atechofficials/espnow-mesh-system/esp32-gateway/gateway_v1/hardware/Development_Resources/esp32-s3/esp32_s3_devkit/ESP32-S3-DEV-KIT-N8R8_Pinout.jpg

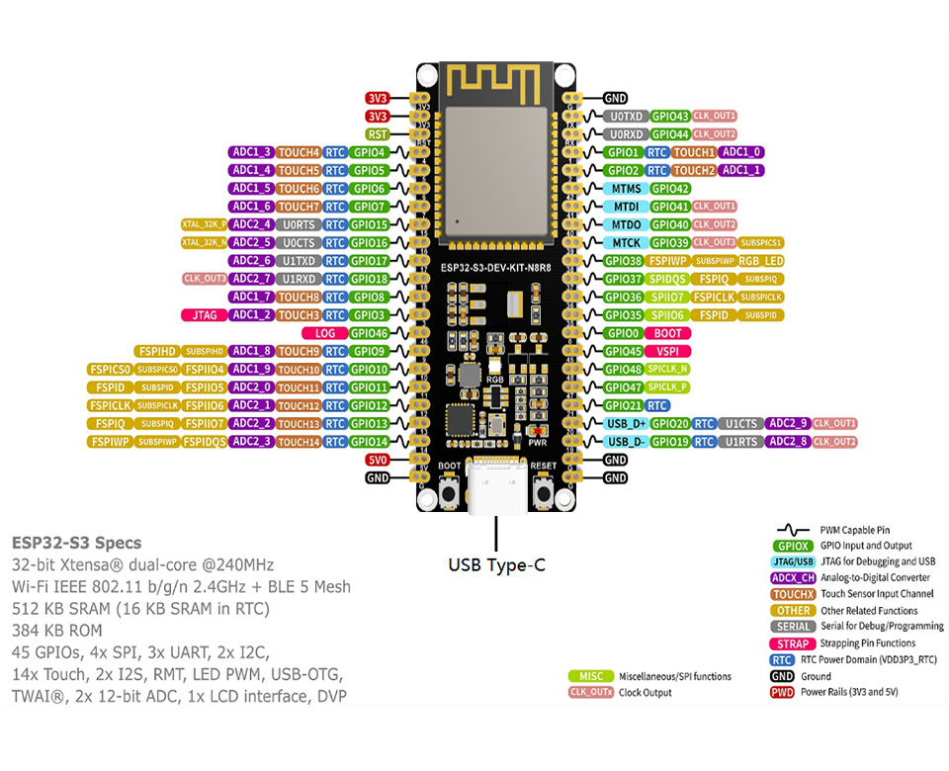
esp32-gateway/gateway_v1/hardware/Development_Resources/esp32-s3/esp32_s3_devkit/ESP32-S3-DEV-KIT-N8R8_Pinout.jpg
