atechofficials/espnow-mesh-system/esp32-gateway/gateway_v1/hardware/Development_Resources/esp32-c3/beetle_esp32_c3/Beetle_ESP32-C3_Overview.png

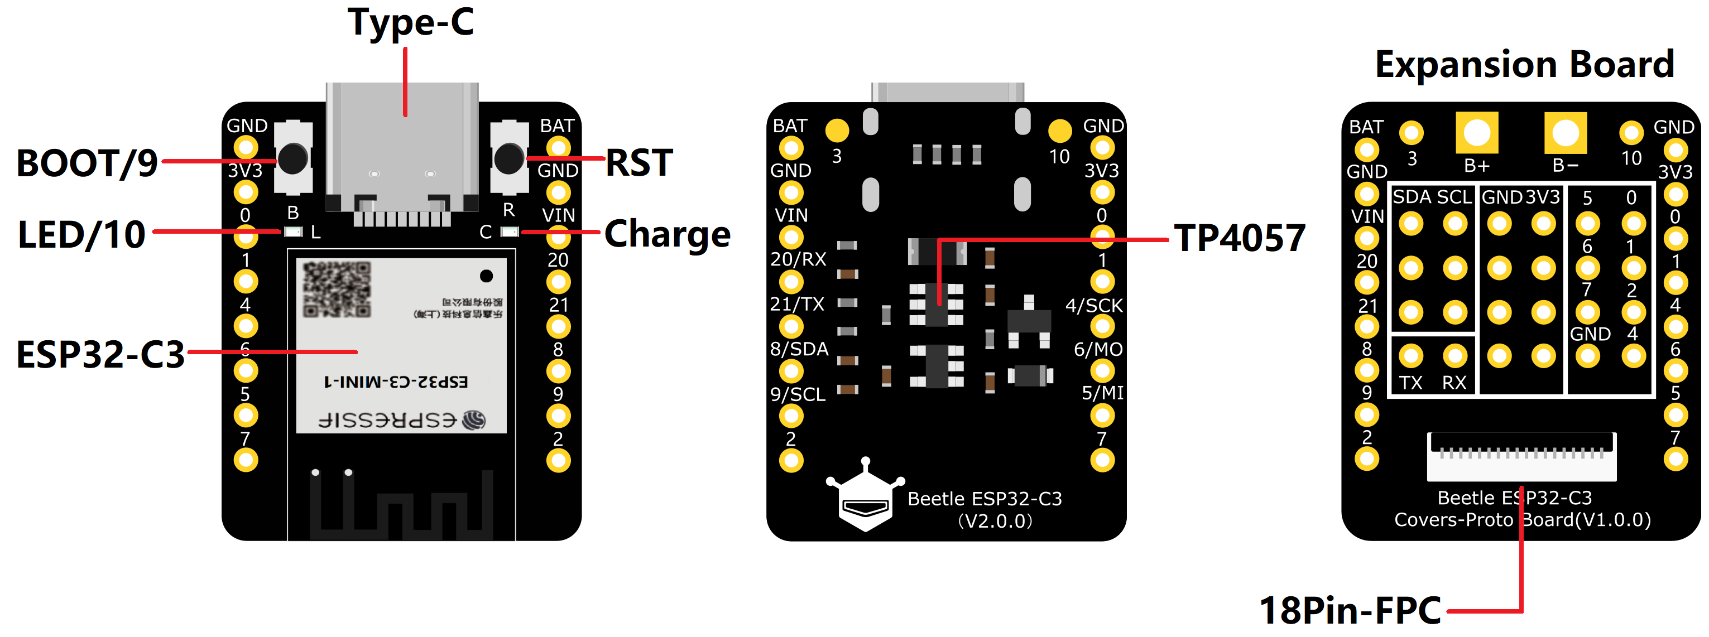
esp32-gateway/gateway_v1/hardware/Development_Resources/esp32-c3/beetle_esp32_c3/Beetle_ESP32-C3_Overview.png
