atechofficials/espnow-mesh-system/esp32-gateway/gateway_v1/src/main.cpp

/**
    * @file [main.cpp]
    * @brief Main source file for the ESP32 Mesh Gateway firmware
 * @version 2.6.7
    * @author Mrinal (@atechofficials)
 */
#define FW_VERSION "2.6.7"

#include <Arduino.h>
#include <WiFi.h>
#include <WiFiClient.h>
#include <WiFiManager.h>
#include <esp_now.h>
#include <esp_wifi.h>
#include <LittleFS.h>
#include <ESPAsyncWebServer.h>
#include <ArduinoJson.h>
#include <PubSubClient.h>
#include <Adafruit_NeoPixel.h>
#include <math.h>
#include <Update.h>
#include <esp_app_format.h>
#include <esp_ota_ops.h>
#include "mesh_protocol.h"
#include "coproc_ota_protocol.h"
#include <Preferences.h>
#include "mbedtls/sha256.h"
#include <algorithm>
#include <ctype.h>
#include <set>
#include "user_config.h"

#if GATEWAY_BUILTIN_SENSOR_ENABLED
    #include <SPI.h>
#endif

#if GATEWAY_BUILTIN_SENSOR_ENABLED
    #include <Adafruit_BME280.h>
    #include <Adafruit_BMP280.h>
#endif

// Other Configuration
#define WEB_PORT         80
#define RELAY_LABEL_MAX_LEN 25
#define OTA_DESC_BUF_LEN (sizeof(esp_image_header_t) + sizeof(esp_image_segment_header_t) + sizeof(esp_app_desc_t))
#define OTA_FW_MARKER "GWFWVER:"
#define OTA_FW_MARKER_LEN 8
#define OTA_FW_VERSION_MAX_LEN 16
#define OTA_HWCFG_MARKER "GWHWCFG:"
#define OTA_HWCFG_MARKER_LEN 8
#define OTA_HWCFG_ID_MAX_LEN HW_CONFIG_ID_LEN
#define OTA_ERROR_MSG_MAX_LEN 192
#define COPROC_BUSY_MSG "Coprocessor Busy. Please try after some time."
#define COPROC_OTA_FW_MARKER "C3FWVER:"
#define COPROC_OTA_FW_MARKER_LEN 8
#define COPROC_OTA_HWCFG_MARKER "C3HWCFG:"
#define COPROC_OTA_HWCFG_MARKER_LEN 8
#define COPROC_OTA_VERSION_MAX_LEN COPROC_FW_VERSION_LEN
#define NODE_OTA_FW_MARKER "NODEFWVER:"
#define NODE_OTA_FW_MARKER_LEN 10
#define NODE_OTA_ROLE_MARKER "NODETYPE:"
#define NODE_OTA_ROLE_MARKER_LEN 9
#define NODE_OTA_HWCFG_MARKER "NODEHWCFG:"
#define NODE_OTA_HWCFG_MARKER_LEN 10
#define NODE_OTA_VERSION_MAX_LEN 16
#define NODE_OTA_FILE_PATH "/node_ota.bin"
#define COPROC_OTA_FILE_PATH "/coproc_ota.bin"
#define NODE_OTA_PORT 80
#define NODE_OTA_AP_CHANNEL 6
#define NODE_OTA_STAGE_TIMEOUT_MS 120000UL
#define NODE_OTA_TRANSFER_TIMEOUT_MS 300000UL
#define NODE_OTA_REJOIN_TIMEOUT_MS 90000UL
#define NODE_OTA_TIMEOUT_RECOVERY_MS 120000UL
#define NODE_OTA_BEGIN_RETRY_MS 2000UL
#define NODE_OTA_BEGIN_MAX_ATTEMPTS 10
#define COPROC_OTA_STAGE_TIMEOUT_MS 120000UL
#define COPROC_OTA_REBOOT_TIMEOUT_MS 90000UL
#define COPROC_UART_BAUD 230400
#define COPROC_UART_RX_BUFFER_SIZE 4096
#define COPROC_UART_TX_BUFFER_SIZE 4096
#define COPROC_LINK_PING_MS 5000UL
#define COPROC_ACK_TIMEOUT_MS 3000UL
#define COPROC_RECOVERY_REBOOT_MS 8000UL
#define COPROC_RECOVERY_COOLDOWN_MS 15000UL
#define COPROC_ACK_RETRY_LIMIT 3
#define COPROC_FRAME_MAX_PAYLOAD sizeof(CoprocUploadChunkPayload)
#define GATEWAY_STA_CONNECT_TIMEOUT_MS 15000UL
#define GATEWAY_NETWORK_MONITOR_MS 2000UL
#define GATEWAY_OFFLINE_RETRY_MS 15000UL
#define GATEWAY_FACTORY_RESET_HOLD_MS 6000UL
#define GATEWAY_FACTORY_RESET_LED_BLINK_MS 300UL
#define MQTT_RECONNECT_MS 10000UL
#define MQTT_BUFFER_SIZE 4096U
#define MQTT_KEEPALIVE_SEC 30U
#define MQTT_SOCKET_TIMEOUT_SEC 5U
#define MQTT_DEFAULT_PORT 1883U
#define MQTT_HA_DISCOVERY_PREFIX "homeassistant"

// Runtime AP credentials - loaded from NVS on boot, fall back to compile-time defaults.
// These are the SSID / password the WiFiManager captive portal AP will use.
static char gwApSsid[33]     = AP_SSID_DEFAULT;
static char gwApPassword[64] = AP_PASS_DEFAULT;
static char gwOfflineSsid[33] = OFFLINE_AP_SSID_DEFAULT;
static char gwOfflinePassword[64] = OFFLINE_AP_PASS_DEFAULT;
static char savedRouterSsid[33] = {0};
static char savedRouterPassword[65] = {0};

// Web Interface Auth
static char webUsername[33]   = "";   // max 32 chars
static char webPassHash[65]   = "";   // SHA-256 hex of password
static char sessionToken[65]  = "";   // generated at login, lives in RAM only
static char rememberToken[65] = "";   // NVS-persisted, used for "Remember Me"
static std::set<uint32_t> authWsClients;  // authenticated WS client IDs

#define RX_QUEUE_SIZE    30
#define WS_UPDATE_MS     2000
#define WS_META_MS       10000
#define DISCOVERED_CLEANUP_MS 1000
#define MAX_DISCOVERED   10
#define RFID_UID_HEX_MAX_LEN ((RFID_UID_MAX_LEN * 2) + 1)

// Node Registry
struct GatewayRfidSlot {
    bool     enabled = false;
    uint8_t  uidLen = 0;
    uint16_t relayMask = 0;
    uint8_t  uid[RFID_UID_MAX_LEN] = {0};
};

struct NodeRecord {
    uint8_t       mac[6];
    NodeType      type;
    uint32_t      capabilities;
    char          name[MESH_NODE_NAME_LEN];
    char          fw_version[8];  // reported by node in MSG_REGISTER
    char          hw_config_id[HW_CONFIG_ID_LEN];  // reported by node in MSG_REGISTER
    unsigned long lastSeen;
    bool          online;
    uint32_t      uptime;
    uint8_t actuatorMask;
    uint8_t       actuatorCount;
    // Per-node dynamic settings schema (populated by MSG_SETTINGS_DATA)
    uint8_t       settingsCount;                     // 0 = not yet received
    SettingDef    settings[NODE_MAX_SETTINGS];        // schema + current values
    // Per-node dynamic sensor schema (populated by MSG_SENSOR_SCHEMA)
    // Indexed by position; sensorSchema[j] and sensorValues[j] are always parallel.
    // sensorCount == 0 means schema has not yet been received from this node.
    uint8_t       sensorCount;                       // 0 = schema not yet received
    SensorDef     sensorSchema[NODE_MAX_SENSORS];    // descriptor for each sensor channel
    float         sensorValues[NODE_MAX_SENSORS];    // last received value per channel
    ActuatorDef   actuatorSchema[NODE_MAX_ACTUATORS];
    char          relayLabels[NODE_MAX_ACTUATORS][RELAY_LABEL_MAX_LEN];
    bool          rfidConfigReady;
    GatewayRfidSlot rfidSlots[RFID_MAX_SLOTS];
    uint8_t       lastRfidUid[RFID_UID_MAX_LEN];
    uint8_t       lastRfidUidLen;
    int8_t        lastRfidMatchedSlot;
    uint16_t      lastRfidAppliedMask;
    unsigned long lastRfidSeenAt;
};
static NodeRecord nodes[MESH_MAX_NODES + 1];
static uint8_t    nextId = 1;
static bool       nodeRegistryDirty = false;
static unsigned long nodeRegistryDirtyAtMs = 0;
static constexpr unsigned long NODE_REGISTRY_FLUSH_MS = 750UL;

// Discovered (beaconing) nodes - not yet paired
struct DiscoveredNode {
    uint8_t       mac[6];
    char          name[MESH_NODE_NAME_LEN];
    NodeType      type;
    uint8_t       tx_channel;  // channel from last beacon
    unsigned long lastSeen;
    bool          active;
};
static DiscoveredNode discovered[MAX_DISCOVERED];

// Pending pair - gateway retries PAIR_CMD until MSG_REGISTER arrives
struct PendingPair {
    uint8_t       mac[6];
    bool          active;
    unsigned long startedAt;
    unsigned long lastAttempt;
};
static PendingPair pendingPair = {};

// RTOS
static SemaphoreHandle_t nodesMutex;

struct RxPacket { uint8_t mac[6]; uint8_t data[250]; int len; };
static QueueHandle_t rxQueue;

// Web Server
static AsyncWebServer server(WEB_PORT);
static AsyncWebSocket ws("/ws");

enum GatewayNetworkMode : uint8_t {
    GATEWAY_SETUP_PORTAL = 0,
    GATEWAY_ONLINE_STA,
    GATEWAY_OFFLINE_AP,
};

// State
static uint8_t   wifiChannel = 1;
static uint32_t  bootMs      = 0;
static GatewayNetworkMode gatewayNetworkMode = GATEWAY_SETUP_PORTAL;
static bool gatewayRouterCredsSaved = false;
static bool gatewayRouterOnline = false;
static bool gatewayOfflineApActive = false;
static bool gatewayManualOfflinePreferred = false;
static bool gatewayForceSetupPortalNextBoot = false;
static bool gatewayOfflineAutoFallback = false;
static uint8_t gatewayLastKnownChannel = OFFLINE_AP_DEFAULT_CHANNEL;
static unsigned long lastGatewayNetworkCheckAt = 0;
static unsigned long lastGatewayRouterRetryAt = 0;
static bool gatewayRouterRetryInProgress = false;
static bool gatewayResetButtonReleased = false;
static bool gatewayResetButtonHandled = false;
static unsigned long gatewayResetButtonPressedAt = 0;
static const IPAddress GATEWAY_OFFLINE_AP_IP(192, 168, 8, 1);
static const IPAddress GATEWAY_OFFLINE_AP_GATEWAY(192, 168, 8, 1);
static const IPAddress GATEWAY_OFFLINE_AP_SUBNET(255, 255, 255, 0);

// Gateway Status LED
static Adafruit_NeoPixel gwLed(1, GW_LED_PIN, GW_LED_COL_ORDER + NEO_KHZ800);
static uint32_t          gwLedCurrent   = 0xDEADBEEF;
static uint32_t          gwLedDesiredColor = 0;
static unsigned long     gwLedFlashUntil = 0;
bool gwLedEnabled = true;
enum GatewayLedOverrideMode : uint8_t {
    GW_LED_OVERRIDE_NONE = 0,
    GW_LED_OVERRIDE_FACTORY_RESET_BLINK,
    GW_LED_OVERRIDE_FACTORY_RESET_SOLID,
};
static GatewayLedOverrideMode gwLedOverrideMode = GW_LED_OVERRIDE_NONE;
static unsigned long     gwLedOverrideLastBlinkAt = 0;
static bool              gwLedOverrideBlinkOn = false;

enum GatewayBuiltinSensorTempUnit : uint8_t {
    GATEWAY_SENSOR_TEMP_C = 0,
    GATEWAY_SENSOR_TEMP_F,
};

enum GatewayBuiltinSensorAltitudeUnit : uint8_t {
    GATEWAY_SENSOR_ALT_M = 0,
    GATEWAY_SENSOR_ALT_FT,
};

enum GatewayBuiltinSensorModel : uint8_t {
    GATEWAY_BUILTIN_SENSOR_MODEL_UNKNOWN = 0,
    GATEWAY_BUILTIN_SENSOR_MODEL_BMP280,
    GATEWAY_BUILTIN_SENSOR_MODEL_BME280,
};

static bool gatewayBuiltinSensorPresent = false;
static GatewayBuiltinSensorModel gatewayBuiltinSensorModel = GATEWAY_BUILTIN_SENSOR_MODEL_UNKNOWN;
static float gatewayBuiltinSensorTempC = NAN;
static float gatewayBuiltinSensorPressureHpa = NAN;
static float gatewayBuiltinSensorHumidity = NAN;
static unsigned long gatewayBuiltinSensorLastSampleAt = 0;
static GatewayBuiltinSensorTempUnit gatewayBuiltinSensorTempUnit = GATEWAY_SENSOR_TEMP_C;
static GatewayBuiltinSensorAltitudeUnit gatewayBuiltinSensorAltitudeUnit = GATEWAY_SENSOR_ALT_M;
static float gatewayBuiltinSensorAltitudeMeters = 0.0f;
static bool gatewayBuiltinSensorAltitudeConfigured = false;

// MQTT Bridge
static WiFiClient mqttNetClient;
static PubSubClient mqttClient(mqttNetClient);
static bool mqttEnabled = false;
static bool mqttConnected = false;
static char mqttHost[65] = {0};
static uint16_t mqttPort = MQTT_DEFAULT_PORT;
static char mqttBaseTopic[97] = "esp32/mesh";
static char mqttUsername[65] = {0};
static char mqttPassword[65] = {0};
static bool mqttHasPassword = false;
static char mqttLastError[128] = {0};
static unsigned long lastMqttReconnectAttemptAt = 0;
static unsigned long lastMqttMetaPublishAt = 0;
static bool mqttRepublishAllPending = false;
static bool mqttMetaDirty = false;
static bool mqttGatewayControlDiscoveryDirty = false;
static bool mqttBuiltinDiscoveryDirty = false;
static bool mqttBuiltinStateDirty = false;
static uint32_t mqttNodeDiscoveryDirtyMask = 0;
static uint32_t mqttNodeSummaryDirtyMask = 0;
static uint32_t mqttNodeSensorStateDirtyMask = 0;
static uint32_t mqttNodeActuatorStateDirtyMask = 0;
static uint32_t mqttNodeSettingsStateDirtyMask = 0;
static uint32_t mqttNodeHeldSensorStateMask[MESH_MAX_NODES + 1] = {0};
static char mqttGatewayTopicId[13] = {0};
static bool mqttLastShouldBeConnected = false;

struct MqttRemovedNodeSnapshot {
    bool active = false;
    char macId[13] = {0};
    bool hadSensors = false;
    uint8_t sensorCount = 0;
    uint8_t sensorIds[NODE_MAX_SENSORS] = {0};
    bool hadActuators = false;
    uint8_t actuatorCount = 0;
    uint8_t actuatorIds[NODE_MAX_ACTUATORS] = {0};
    uint8_t settingsCount = 0;
    uint8_t settingIds[NODE_MAX_SETTINGS] = {0};
    SettingType settingTypes[NODE_MAX_SETTINGS] = {};
};
static MqttRemovedNodeSnapshot mqttRemovedNodes[MESH_MAX_NODES];

#if GATEWAY_BUILTIN_SENSOR_ENABLED
static SPIClass gatewayBuiltinSensorSpi(FSPI);
static bool gatewayBuiltinSensorSpiReady = false;
static Adafruit_BME280 gatewayBuiltinBme(BME_CS, &gatewayBuiltinSensorSpi);
static Adafruit_BMP280 gatewayBuiltinBmp(BME_CS, &gatewayBuiltinSensorSpi);
#endif

__attribute__((used)) static const char kGatewayFirmwareVersionMarker[] = OTA_FW_MARKER FW_VERSION;
__attribute__((used)) static const char kGatewayHardwareConfigMarker[] = OTA_HWCFG_MARKER HW_CONFIG_ID;
static volatile uint32_t gGatewayFirmwareMarkerChecksum = 0;

static void touchGatewayFirmwareMarkers() {
    uint32_t sum = 0;
    for (size_t i = 0; kGatewayFirmwareVersionMarker[i] != '\0'; i++) {
        sum += (uint8_t)kGatewayFirmwareVersionMarker[i];
    }
    for (size_t i = 0; kGatewayHardwareConfigMarker[i] != '\0'; i++) {
        sum += (uint8_t)kGatewayHardwareConfigMarker[i];
    }
    gGatewayFirmwareMarkerChecksum = sum;
}

struct GatewayOtaRequestState {
    bool   started = false;
    bool   ok = false;
    bool   updateBegun = false;
    bool   metadataValidated = false;
    bool   descFlushed = false;
    size_t expectedSize = 0;
    size_t written = 0;
    char   filename[64] = {0};
    char   incomingVersion[33] = {0};
    char   incomingDisplayVersion[OTA_FW_VERSION_MAX_LEN] = {0};
    char   incomingHwConfigId[OTA_HWCFG_ID_MAX_LEN] = {0};
    char   error[OTA_ERROR_MSG_MAX_LEN] = {0};
    uint8_t descBuf[OTA_DESC_BUF_LEN] = {0};
    size_t descBytes = 0;
    uint8_t markerMatchIndex = 0;
    bool    markerReadingVersion = false;
    uint8_t markerVersionLen = 0;
    uint8_t hwMarkerMatchIndex = 0;
    bool    hwMarkerReading = false;
    uint8_t hwMarkerLen = 0;
};

enum CoprocOtaJobStage : uint8_t {
    COPROC_OTA_JOB_IDLE = 0,
    COPROC_OTA_JOB_STAGED,
    COPROC_OTA_JOB_WAIT_HELLO,
    COPROC_OTA_JOB_BEGIN,
    COPROC_OTA_JOB_STREAM,
    COPROC_OTA_JOB_FINALIZE,
    COPROC_OTA_JOB_WAIT_REBOOT,
    COPROC_OTA_JOB_SUCCESS,
    COPROC_OTA_JOB_ERROR,
};

struct CoprocOtaUploadRequestState {
    bool   started = false;
    bool   ok = false;
    bool   metadataValidated = false;
    size_t expectedSize = 0;
    size_t written = 0;
    uint32_t crc32 = 0xFFFFFFFFu;
    char   filename[64] = {0};
    char   incomingVersion[33] = {0};
    char   incomingDisplayVersion[COPROC_OTA_VERSION_MAX_LEN] = {0};
    char   incomingHwConfigId[HW_CONFIG_ID_LEN] = {0};
    char   incomingProjectName[COPROC_PROJECT_NAME_LEN] = {0};
    char   error[OTA_ERROR_MSG_MAX_LEN] = {0};
    uint8_t descBuf[OTA_DESC_BUF_LEN] = {0};
    size_t descBytes = 0;
    uint8_t versionMarkerMatchIndex = 0;
    bool    versionMarkerReading = false;
    uint8_t versionMarkerLen = 0;
    uint8_t hwMarkerMatchIndex = 0;
    bool    hwMarkerReading = false;
    uint8_t hwMarkerLen = 0;
    File    file;
};

static bool          otaUploadBusy    = false;
static bool          otaRebootPending = false;
static unsigned long otaRebootAtMs    = 0;

enum NodeOtaJobStage : uint8_t {
    NODE_OTA_JOB_IDLE = 0,
    NODE_OTA_JOB_STAGED,
    NODE_OTA_JOB_COPROC_WAIT,
    NODE_OTA_JOB_COPROC_BEGIN,
    NODE_OTA_JOB_COPROC_STREAM,
    NODE_OTA_JOB_COPROC_FINALIZE,
    NODE_OTA_JOB_SEND_COMMAND,
    NODE_OTA_JOB_WAIT_TRANSFER,
    NODE_OTA_JOB_WAIT_REJOIN,
    NODE_OTA_JOB_SUCCESS,
    NODE_OTA_JOB_ERROR,
};

struct NodeOtaUploadRequestState {
    bool   started = false;
    bool   ok = false;
    bool   metadataValidated = false;
    bool   descFlushed = false;
    size_t expectedSize = 0;
    size_t written = 0;
    uint32_t crc32 = 0xFFFFFFFFu;
    char   filename[64] = {0};
    char   incomingVersion[NODE_OTA_VERSION_MAX_LEN] = {0};
    char   incomingDisplayVersion[NODE_OTA_VERSION_MAX_LEN] = {0};
    char   incomingRole[16] = {0};
    char   incomingHwConfigId[HW_CONFIG_ID_LEN] = {0};
    char   error[OTA_ERROR_MSG_MAX_LEN] = {0};
    uint8_t descBuf[OTA_DESC_BUF_LEN] = {0};
    size_t descBytes = 0;
    uint8_t versionMarkerMatchIndex = 0;
    bool    versionMarkerReading = false;
    uint8_t versionMarkerLen = 0;
    uint8_t roleMarkerMatchIndex = 0;
    bool    roleMarkerReading = false;
    uint8_t roleMarkerLen = 0;
    uint8_t hwMarkerMatchIndex = 0;
    bool    hwMarkerReading = false;
    uint8_t hwMarkerLen = 0;
    File    file;
};

struct NodeOtaJobState {
    bool           active = false;
    bool           uploadBusy = false;
    bool           helperOnline = false;
    bool           awaitingAck = false;
    bool           helperApReady = false;
    bool           helperTransferDone = false;
    bool           nodeAccepted = false;
    uint8_t        awaitingFrameType = 0;
    uint8_t        nodeId = 0;
    NodeType       targetType = NODE_SENSOR;
    NodeOtaJobStage stage = NODE_OTA_JOB_IDLE;
    uint32_t       sessionId = 0;
    uint32_t       imageCrc32 = 0;
    size_t         imageSize = 0;
    size_t         uploadOffset = 0;
    unsigned long  lastCommandAt = 0;
    unsigned long  stageStartedAt = 0;
    unsigned long  lastActivityAt = 0;
    unsigned long  lastAckAt = 0;
    uint8_t        coprocAckRetries = 0;
    uint8_t        commandAttempts = 0;
    char           version[NODE_OTA_VERSION_MAX_LEN] = {0};
    char           priorVersion[8] = {0};
    char           filename[64] = {0};
    char           message[96] = {0};
    char           error[128] = {0};
    char           apSsid[NODE_OTA_SSID_LEN] = {0};
    char           apPassword[NODE_OTA_PASS_LEN] = {0};
    uint8_t        progress = 0;
    File           file;
};

struct CoprocOtaJobState {
    bool           active = false;
    bool           uploadBusy = false;
    bool           awaitingAck = false;
    bool           rebootSeen = false;
    bool           flashReportedDone = false;
    uint8_t        awaitingFrameType = 0;
    CoprocOtaJobStage stage = COPROC_OTA_JOB_IDLE;
    uint32_t       sessionId = 0;
    uint32_t       imageCrc32 = 0;
    size_t         imageSize = 0;
    size_t         uploadOffset = 0;
    unsigned long  stageStartedAt = 0;
    unsigned long  lastActivityAt = 0;
    unsigned long  lastAckAt = 0;
    uint8_t        ackRetries = 0;
    char           version[COPROC_OTA_VERSION_MAX_LEN] = {0};
    char           priorVersion[COPROC_FW_VERSION_LEN] = {0};
    char           filename[64] = {0};
    char           message[96] = {0};
    char           error[128] = {0};
    uint8_t        progress = 0;
    File           file;
};

struct CoprocAckState {
    bool     ready = false;
    uint8_t  originalType = 0;
    bool     ok = false;
    uint32_t value = 0;
    char     message[COPROC_STATUS_MESSAGE_LEN] = {0};
};

struct CoprocRxState {
    enum State : uint8_t {
        WAIT_MAGIC_1 = 0,
        WAIT_MAGIC_2,
        READ_TYPE,
        READ_LEN_1,
        READ_LEN_2,
        READ_PAYLOAD,
        READ_CRC_1,
        READ_CRC_2,
    } state = WAIT_MAGIC_1;
    uint8_t  type = 0;
    uint16_t length = 0;
    uint16_t expectedCrc = 0;
    uint16_t payloadIndex = 0;
    uint8_t  payload[COPROC_FRAME_MAX_PAYLOAD] = {0};
};

static HardwareSerial coprocSerial(1);
static NodeOtaJobState nodeOtaJob;
static CoprocOtaJobState coprocOtaJob;
static CoprocAckState coprocAck;
static CoprocRxState coprocRx;
static unsigned long lastCoprocHelloAt = 0;
static bool coprocOnline = false;
static unsigned long lastCoprocAckAt = 0;
static unsigned long lastCoprocNoAckLogAt = 0;
static unsigned long lastCoprocRecoveryPulseAt = 0;
static bool coprocOtaSupportedRemote = false;
static bool espNowReady = false;
static uint32_t coprocOtaMaxBytes = 0;
static char coprocFwVersion[COPROC_FW_VERSION_LEN] = {0};
static char coprocHwConfigId[COPROC_HWCFG_ID_LEN] = {0};
static char coprocProjectName[COPROC_PROJECT_NAME_LEN] = {0};

// *****************************************************************************
// Gateway Status LED Helpers
// *****************************************************************************
static void applyGwLedHardware(uint32_t color) {
    if (color == gwLedCurrent) return;
    gwLedCurrent = color;
    gwLed.setPixelColor(0, color);
    gwLed.show();
}

static void setGwLed(uint32_t color) {
    gwLedDesiredColor = color;
    if (gwLedOverrideMode != GW_LED_OVERRIDE_NONE) return;
    applyGwLedHardware(color);
}

static void startGatewayFactoryResetLedBlink(unsigned long now) {
    gwLedOverrideMode = GW_LED_OVERRIDE_FACTORY_RESET_BLINK;
    gwLedOverrideLastBlinkAt = now;
    gwLedOverrideBlinkOn = true;
    applyGwLedHardware(gwLed.Color(160, 60, 0));  // dark orange
}

static void showGatewayFactoryResetLedConfirm() {
    gwLedOverrideMode = GW_LED_OVERRIDE_FACTORY_RESET_SOLID;
    gwLedOverrideBlinkOn = true;
    applyGwLedHardware(gwLed.Color(255, 0, 0));  // solid red
}

static void clearGatewayLedOverride() {
    if (gwLedOverrideMode == GW_LED_OVERRIDE_NONE) return;
    gwLedOverrideMode = GW_LED_OVERRIDE_NONE;
    gwLedOverrideBlinkOn = false;
    gwLedCurrent = 0xDEADBEEF;  // force immediate repaint from normal state
    if (!gwLedEnabled) {
        applyGwLedHardware(0);
        return;
    }
    if (millis() < gwLedFlashUntil) {
        applyGwLedHardware(gwLedDesiredColor);
        return;
    }
    setGwLed(gwLed.Color(0, 0, 32));  // resume normal operational color
}

static void flashGwLed(uint32_t color, uint32_t durationMs) {
    gwLedFlashUntil = millis() + durationMs;
    setGwLed(color);
    gwLedCurrent = 0xDEADBEEF;  // force refresh after flash
}

static void updateGwLed() {
    const unsigned long now = millis();

    if (gwLedOverrideMode == GW_LED_OVERRIDE_FACTORY_RESET_SOLID) {
        applyGwLedHardware(gwLed.Color(255, 0, 0));
        return;
    }

    if (gwLedOverrideMode == GW_LED_OVERRIDE_FACTORY_RESET_BLINK) {
        if ((now - gwLedOverrideLastBlinkAt) >= GATEWAY_FACTORY_RESET_LED_BLINK_MS) {
            gwLedOverrideLastBlinkAt = now;
            gwLedOverrideBlinkOn = !gwLedOverrideBlinkOn;
        }
        applyGwLedHardware(gwLedOverrideBlinkOn ? gwLed.Color(160, 60, 0) : 0);
        return;
    }

    if (!gwLedEnabled) {
        applyGwLedHardware(0);
        return;
    }
    if (now < gwLedFlashUntil) {
        applyGwLedHardware(gwLedDesiredColor);
        return;
    }
    setGwLed(gwLed.Color(0, 0, 32));  // dim blue = operational
}

static void saveGwLedState(bool enabled) {
    Preferences prefs;
    prefs.begin("gwconfig", false);  // read-write
    prefs.putBool("led_enabled", enabled);
    prefs.end();
    gwLedEnabled = enabled;
    if (!enabled && gwLedOverrideMode == GW_LED_OVERRIDE_NONE) {
        setGwLed(0);  // turn off immediately
    }
}

static void loadGwLedState() {
    Preferences prefs;
    prefs.begin("gwconfig", true);  // read-only
    gwLedEnabled = prefs.getBool("led_enabled", true);
    prefs.end();
    Serial.printf("[CFG]  Gateway LED is %s\n", gwLedEnabled ? "enabled" : "disabled");
    if (!gwLedEnabled && gwLedOverrideMode == GW_LED_OVERRIDE_NONE) {
        setGwLed(0);
    }
}

// *****************************************************************************
//  Gateway Built-in Sensor Helpers
// *****************************************************************************
static void mqttMarkBuiltinDiscoveryDirty();
static void mqttMarkBuiltinStateDirty();
static void mqttMarkMetaDirty();

static bool gatewayBuiltinSensorFeatureEnabled() {
    return GATEWAY_BUILTIN_SENSOR_ENABLED;
}

static const char* gatewayBuiltinSensorModelString() {
    if (!gatewayBuiltinSensorFeatureEnabled()) return "disabled";
    switch (gatewayBuiltinSensorModel) {
        case GATEWAY_BUILTIN_SENSOR_MODEL_BME280: return "bme280";
        case GATEWAY_BUILTIN_SENSOR_MODEL_BMP280: return "bmp280";
        default: return "auto";
    }
}

static bool gatewayBuiltinSensorSupportsHumidity() {
    return gatewayBuiltinSensorModel == GATEWAY_BUILTIN_SENSOR_MODEL_BME280;
}

static const char* gatewayBuiltinSensorTempUnitString() {
    return gatewayBuiltinSensorTempUnit == GATEWAY_SENSOR_TEMP_F ? "F" : "C";
}

static const char* gatewayBuiltinSensorAltitudeUnitString() {
    return gatewayBuiltinSensorAltitudeUnit == GATEWAY_SENSOR_ALT_FT ? "ft" : "m";
}

static bool parseGatewayBuiltinTempUnit(const char* value,
                                        GatewayBuiltinSensorTempUnit* outUnit) {
    if (!outUnit || !value) return false;
    if (strcmp(value, "F") == 0 || strcmp(value, "f") == 0) {
        *outUnit = GATEWAY_SENSOR_TEMP_F;
        return true;
    }
    if (strcmp(value, "C") == 0 || strcmp(value, "c") == 0) {
        *outUnit = GATEWAY_SENSOR_TEMP_C;
        return true;
    }
    return false;
}

static bool parseGatewayBuiltinAltitudeUnit(const char* value,
                                            GatewayBuiltinSensorAltitudeUnit* outUnit) {
    if (!outUnit || !value) return false;
    if (strcmp(value, "ft") == 0 || strcmp(value, "FT") == 0 ||
        strcmp(value, "feet") == 0 || strcmp(value, "Feet") == 0) {
        *outUnit = GATEWAY_SENSOR_ALT_FT;
        return true;
    }
    if (strcmp(value, "m") == 0 || strcmp(value, "M") == 0 ||
        strcmp(value, "meter") == 0 || strcmp(value, "meters") == 0) {
        *outUnit = GATEWAY_SENSOR_ALT_M;
        return true;
    }
    return false;
}

static float gatewayBuiltinAltitudeDisplayValue() {
    if (!isfinite(gatewayBuiltinSensorAltitudeMeters)) return 0.0f;
    if (gatewayBuiltinSensorAltitudeUnit == GATEWAY_SENSOR_ALT_FT) {
        return gatewayBuiltinSensorAltitudeMeters * 3.2808399f;
    }
    return gatewayBuiltinSensorAltitudeMeters;
}

static float gatewayBuiltinAltitudeMetersFromDisplay(float value,
                                                     GatewayBuiltinSensorAltitudeUnit unit) {
    if (!isfinite(value)) return 0.0f;
    return unit == GATEWAY_SENSOR_ALT_FT ? (value / 3.2808399f) : value;
}

static float gatewayBuiltinDisplayTemperature() {
    if (!isfinite(gatewayBuiltinSensorTempC)) return NAN;
    if (gatewayBuiltinSensorTempUnit == GATEWAY_SENSOR_TEMP_F) {
        return (gatewayBuiltinSensorTempC * 9.0f / 5.0f) + 32.0f;
    }
    return gatewayBuiltinSensorTempC;
}

static float gatewayBuiltinSeaLevelPressureHpa() {
    if (!isfinite(gatewayBuiltinSensorPressureHpa) || gatewayBuiltinSensorPressureHpa <= 0.0f) {
        return NAN;
    }
    const float ratio = 1.0f - (gatewayBuiltinSensorAltitudeMeters / 44330.0f);
    if (ratio <= 0.0f) return gatewayBuiltinSensorPressureHpa;
    return gatewayBuiltinSensorPressureHpa / powf(ratio, 5.255f);
}

static void loadGatewayBuiltinSensorSettings() {
    Preferences prefs;
    prefs.begin("gwconfig", true);
    const uint8_t tempUnit = prefs.isKey("bs_temp_u")
        ? prefs.getUChar("bs_temp_u", (uint8_t)GATEWAY_SENSOR_TEMP_C)
        : (uint8_t)GATEWAY_SENSOR_TEMP_C;
    const uint8_t altitudeUnit = prefs.isKey("bs_alt_u")
        ? prefs.getUChar("bs_alt_u", (uint8_t)GATEWAY_SENSOR_ALT_M)
        : (uint8_t)GATEWAY_SENSOR_ALT_M;
    const bool altitudeConfigured = prefs.isKey("bs_alt_m");
    const float altitudeMeters = altitudeConfigured ? prefs.getFloat("bs_alt_m", 0.0f) : 0.0f;
    prefs.end();

    gatewayBuiltinSensorTempUnit = tempUnit == (uint8_t)GATEWAY_SENSOR_TEMP_F
        ? GATEWAY_SENSOR_TEMP_F
        : GATEWAY_SENSOR_TEMP_C;
    gatewayBuiltinSensorAltitudeUnit = altitudeUnit == (uint8_t)GATEWAY_SENSOR_ALT_FT
        ? GATEWAY_SENSOR_ALT_FT
        : GATEWAY_SENSOR_ALT_M;
    gatewayBuiltinSensorAltitudeMeters = isfinite(altitudeMeters)
        ? constrain(altitudeMeters, -500.0f, 10000.0f)
        : 0.0f;
    gatewayBuiltinSensorAltitudeConfigured = altitudeConfigured;
}

static void saveGatewayBuiltinSensorSettings(GatewayBuiltinSensorTempUnit tempUnit,
                                             GatewayBuiltinSensorAltitudeUnit altitudeUnit,
                                             float altitudeMeters) {
    Preferences prefs;
    prefs.begin("gwconfig", false);
    prefs.putUChar("bs_temp_u", (uint8_t)tempUnit);
    prefs.putUChar("bs_alt_u", (uint8_t)altitudeUnit);
    prefs.putFloat("bs_alt_m", altitudeMeters);
    prefs.end();

    gatewayBuiltinSensorTempUnit = tempUnit;
    gatewayBuiltinSensorAltitudeUnit = altitudeUnit;
    gatewayBuiltinSensorAltitudeMeters = altitudeMeters;
    gatewayBuiltinSensorAltitudeConfigured = true;
    mqttMarkBuiltinDiscoveryDirty();
    mqttMarkBuiltinStateDirty();
    mqttMarkMetaDirty();
}

#if GATEWAY_BUILTIN_SENSOR_ENABLED
static bool gatewayBuiltinSensorEnsureSpiReady() {
    if (gatewayBuiltinSensorSpiReady) return true;

    pinMode(BME_CS, OUTPUT);
    digitalWrite(BME_CS, HIGH);
    gatewayBuiltinSensorSpiReady = gatewayBuiltinSensorSpi.begin(BME_SCK, BME_MISO, BME_MOSI, BME_CS);
    if (!gatewayBuiltinSensorSpiReady) {
        Serial.printf("[GW SENS] Failed to start SPI bus for built-in %s (SCK=%d MISO=%d MOSI=%d CS=%d).\n",
                      gatewayBuiltinSensorModelString(), BME_SCK, BME_MISO, BME_MOSI, BME_CS);
        return false;
    }
    delay(2);
    return true;
}

static uint8_t gatewayBuiltinSensorReadSpiReg(uint8_t reg, uint8_t dataMode) {
    if (!gatewayBuiltinSensorEnsureSpiReady()) return 0xFF;

    gatewayBuiltinSensorSpi.beginTransaction(SPISettings(1000000, MSBFIRST, dataMode));
    digitalWrite(BME_CS, LOW);
    gatewayBuiltinSensorSpi.transfer(reg | 0x80);
    const uint8_t value = gatewayBuiltinSensorSpi.transfer(0x00);
    digitalWrite(BME_CS, HIGH);
    gatewayBuiltinSensorSpi.endTransaction();
    return value;
}

static const char* gatewayBuiltinSensorChipIdDescription(uint8_t chipId) {
    switch (chipId) {
        case 0x60: return "BME280";
        case 0x58: return "BMP280";
        case 0x56:
        case 0x57: return "BMP280-family";
        case 0x00: return "no SPI response (stuck low)";
        case 0xFF: return "no SPI response (stuck high)";
        default:   return "unknown response";
    }
}

static GatewayBuiltinSensorModel gatewayBuiltinSensorModelFromChipId(uint8_t chipId) {
    switch (chipId) {
        case 0x60: return GATEWAY_BUILTIN_SENSOR_MODEL_BME280;
        case 0x56:
        case 0x57:
        case 0x58: return GATEWAY_BUILTIN_SENSOR_MODEL_BMP280;
        default:   return GATEWAY_BUILTIN_SENSOR_MODEL_UNKNOWN;
    }
}

static void logGatewayBuiltinSensorProbe() {
    if (!gatewayBuiltinSensorEnsureSpiReady()) return;

    const uint8_t chipIdMode0 = gatewayBuiltinSensorReadSpiReg(0xD0, SPI_MODE0);
    const uint8_t chipIdMode3 = gatewayBuiltinSensorReadSpiReg(0xD0, SPI_MODE3);
    Serial.printf("[GW SENS] SPI probe for built-in sensor on SCK=%d MISO=%d MOSI=%d CS=%d -> mode0=0x%02X (%s), mode3=0x%02X (%s)\n",
                  BME_SCK, BME_MISO, BME_MOSI, BME_CS,
                  chipIdMode0, gatewayBuiltinSensorChipIdDescription(chipIdMode0),
                  chipIdMode3, gatewayBuiltinSensorChipIdDescription(chipIdMode3));
    const GatewayBuiltinSensorModel probeModel =
        gatewayBuiltinSensorModelFromChipId(chipIdMode0) != GATEWAY_BUILTIN_SENSOR_MODEL_UNKNOWN
            ? gatewayBuiltinSensorModelFromChipId(chipIdMode0)
            : gatewayBuiltinSensorModelFromChipId(chipIdMode3);
    if (probeModel == GATEWAY_BUILTIN_SENSOR_MODEL_BME280) {
        Serial.println("[GW SENS] Probe suggests the module is replying as BME280.");
    } else if (probeModel == GATEWAY_BUILTIN_SENSOR_MODEL_BMP280) {
        Serial.println("[GW SENS] Probe suggests the module is replying as BMP280.");
    }
}
#endif

static bool initGatewayBuiltinSensor() {
    bool spiReady = true;
#if GATEWAY_BUILTIN_SENSOR_ENABLED
    spiReady = gatewayBuiltinSensorEnsureSpiReady();
#endif

    if (!gatewayBuiltinSensorFeatureEnabled()) {
        gatewayBuiltinSensorPresent = false;
        gatewayBuiltinSensorModel = GATEWAY_BUILTIN_SENSOR_MODEL_UNKNOWN;
        gatewayBuiltinSensorTempC = NAN;
        gatewayBuiltinSensorPressureHpa = NAN;
        gatewayBuiltinSensorHumidity = NAN;
        mqttMarkBuiltinDiscoveryDirty();
        mqttMarkBuiltinStateDirty();
        mqttMarkMetaDirty();
        return false;
    }

    gatewayBuiltinSensorPresent = false;
    gatewayBuiltinSensorModel = GATEWAY_BUILTIN_SENSOR_MODEL_UNKNOWN;
    gatewayBuiltinSensorTempC = NAN;
    gatewayBuiltinSensorPressureHpa = NAN;
    gatewayBuiltinSensorHumidity = NAN;

#if GATEWAY_BUILTIN_SENSOR_ENABLED
    uint8_t chipIdMode0 = 0xFF;
    uint8_t chipIdMode3 = 0xFF;
    if (spiReady) {
        chipIdMode0 = gatewayBuiltinSensorReadSpiReg(0xD0, SPI_MODE0);
        chipIdMode3 = gatewayBuiltinSensorReadSpiReg(0xD0, SPI_MODE3);
        gatewayBuiltinSensorModel =
            gatewayBuiltinSensorModelFromChipId(chipIdMode0) != GATEWAY_BUILTIN_SENSOR_MODEL_UNKNOWN
                ? gatewayBuiltinSensorModelFromChipId(chipIdMode0)
                : gatewayBuiltinSensorModelFromChipId(chipIdMode3);

        switch (gatewayBuiltinSensorModel) {
            case GATEWAY_BUILTIN_SENSOR_MODEL_BME280:
                gatewayBuiltinSensorPresent = gatewayBuiltinBme.begin();
                break;
            case GATEWAY_BUILTIN_SENSOR_MODEL_BMP280:
                gatewayBuiltinSensorPresent = gatewayBuiltinBmp.begin();
                break;
            default:
                gatewayBuiltinSensorPresent = false;
                break;
        }
    }
#endif

    if (gatewayBuiltinSensorPresent) {
        Serial.printf("[GW SENS] Built-in %s detected on SPI.\n", gatewayBuiltinSensorModelString());
    } else {
        if (gatewayBuiltinSensorModel != GATEWAY_BUILTIN_SENSOR_MODEL_UNKNOWN) {
            Serial.printf("[GW SENS] Built-in %s probe succeeded, but driver init failed.\n",
                          gatewayBuiltinSensorModelString());
        } else {
            Serial.println("[GW SENS] Built-in BMP280/BME280 sensor not detected.");
        }
#if GATEWAY_BUILTIN_SENSOR_ENABLED
        logGatewayBuiltinSensorProbe();
#endif
    }
    mqttMarkBuiltinDiscoveryDirty();
    mqttMarkBuiltinStateDirty();
    mqttMarkMetaDirty();
    return gatewayBuiltinSensorPresent;
}

static bool sampleGatewayBuiltinSensor() {
    if (!gatewayBuiltinSensorFeatureEnabled() || !gatewayBuiltinSensorPresent) return false;
    gatewayBuiltinSensorLastSampleAt = millis();

    float tempC = NAN;
    float pressurePa = NAN;
    float humidity = NAN;
    switch (gatewayBuiltinSensorModel) {
        case GATEWAY_BUILTIN_SENSOR_MODEL_BME280:
            tempC = gatewayBuiltinBme.readTemperature();
            pressurePa = gatewayBuiltinBme.readPressure();
            humidity = gatewayBuiltinBme.readHumidity();
            break;
        case GATEWAY_BUILTIN_SENSOR_MODEL_BMP280:
            tempC = gatewayBuiltinBmp.readTemperature();
            pressurePa = gatewayBuiltinBmp.readPressure();
            humidity = NAN;
            break;
        default:
            return false;
    }

    if (!isfinite(tempC) || !isfinite(pressurePa) || pressurePa <= 0.0f) {
        Serial.println("[GW SENS] Built-in sensor read failed.");
        return false;
    }

    gatewayBuiltinSensorTempC = tempC;
    gatewayBuiltinSensorPressureHpa = pressurePa / 100.0f;
    gatewayBuiltinSensorHumidity = isfinite(humidity) ? humidity : NAN;
    mqttMarkBuiltinStateDirty();
    mqttMarkMetaDirty();
    return true;
}

static void sampleGatewayBuiltinSensorIfDue(unsigned long now) {
    if (!gatewayBuiltinSensorFeatureEnabled() || !gatewayBuiltinSensorPresent) return;
    if (gatewayBuiltinSensorLastSampleAt == 0 ||
        (now - gatewayBuiltinSensorLastSampleAt) >= WS_META_MS) {
        sampleGatewayBuiltinSensor();
    }
}

// *****************************************************************************
//  Helpers
// *****************************************************************************
static String macToStr(const uint8_t* mac) {
    char buf[18];
    snprintf(buf, sizeof(buf), "%02X:%02X:%02X:%02X:%02X:%02X",
             mac[0], mac[1], mac[2], mac[3], mac[4], mac[5]);
    return String(buf);
}

static unsigned long elapsedSinceMs(unsigned long now, unsigned long then) {
    return (now >= then) ? (now - then) : 0UL;
}

static bool parseMac(const char* str, uint8_t* mac) {
    return sscanf(str, "%hhx:%hhx:%hhx:%hhx:%hhx:%hhx",
                  &mac[0], &mac[1], &mac[2], &mac[3], &mac[4], &mac[5]) == 6;
}

static void defaultRelayLabel(uint8_t relayIdx, char* out, size_t outSize) {
    snprintf(out, outSize, "Relay %u", relayIdx + 1);
}

static void resetRelayLabels(char labels[NODE_MAX_ACTUATORS][RELAY_LABEL_MAX_LEN]) {
    for (uint8_t i = 0; i < NODE_MAX_ACTUATORS; i++) {
        defaultRelayLabel(i, labels[i], RELAY_LABEL_MAX_LEN);
    }
}

static void sanitizeRelayLabel(const char* input, uint8_t relayIdx,
                               char* out, size_t outSize) {
    String label = input ? String(input) : String();
    label.trim();
    if (label.length() == 0) {
        defaultRelayLabel(relayIdx, out, outSize);
        return;
    }
    label.replace("\r", " ");
    label.replace("\n", " ");
    while (label.indexOf("  ") >= 0) label.replace("  ", " ");
    strncpy(out, label.c_str(), outSize - 1);
    out[outSize - 1] = '\0';
}

static void buildRelayLabelPrefKey(const uint8_t* mac, char* key, size_t keySize) {
    snprintf(key, keySize, "%02X%02X%02X%02X%02X%02X",
             mac[0], mac[1], mac[2], mac[3], mac[4], mac[5]);
}

struct RelayLabelRecordV1 {
    char labels[4][RELAY_LABEL_MAX_LEN];
};

struct RelayLabelRecordV2 {
    char labels[NODE_MAX_ACTUATORS][RELAY_LABEL_MAX_LEN];
};

static void loadRelayLabelsForNode(uint8_t nodeId) {
    if (nodeId == 0 || nodeId > MESH_MAX_NODES) return;
    resetRelayLabels(nodes[nodeId].relayLabels);
    if (nodes[nodeId].mac[0] == 0 && nodes[nodeId].mac[1] == 0) return;

    RelayLabelRecordV2 rec{};
    char key[13];
    buildRelayLabelPrefKey(nodes[nodeId].mac, key, sizeof(key));

    Preferences prefs;
    prefs.begin("gwrelay", true);
    const size_t blobLen = prefs.getBytesLength(key);
    size_t got = 0;
    if (blobLen == sizeof(RelayLabelRecordV2)) {
        got = prefs.getBytes(key, &rec, sizeof(rec));
    } else if (blobLen == sizeof(RelayLabelRecordV1)) {
        RelayLabelRecordV1 legacy{};
        got = prefs.getBytes(key, &legacy, sizeof(legacy));
        if (got == sizeof(legacy)) {
            for (uint8_t i = 0; i < 4; i++) {
                memcpy(rec.labels[i], legacy.labels[i], sizeof(legacy.labels[i]));
            }
        }
    }
    prefs.end();

    if (got != sizeof(rec) && got != sizeof(RelayLabelRecordV1)) return;

    for (uint8_t i = 0; i < NODE_MAX_ACTUATORS; i++) {
        sanitizeRelayLabel(rec.labels[i], i, nodes[nodeId].relayLabels[i], RELAY_LABEL_MAX_LEN);
    }
}

static void saveRelayLabelsForNode(uint8_t nodeId) {
    if (nodeId == 0 || nodeId > MESH_MAX_NODES) return;
    if (nodes[nodeId].mac[0] == 0 && nodes[nodeId].mac[1] == 0) return;

    RelayLabelRecordV2 rec{};
    for (uint8_t i = 0; i < NODE_MAX_ACTUATORS; i++) {
        sanitizeRelayLabel(nodes[nodeId].relayLabels[i], i, rec.labels[i], RELAY_LABEL_MAX_LEN);
    }

    char key[13];
    buildRelayLabelPrefKey(nodes[nodeId].mac, key, sizeof(key));

    Preferences prefs;
    prefs.begin("gwrelay", false);
    prefs.putBytes(key, &rec, sizeof(rec));
    prefs.end();
}

static void removeRelayLabelsForMac(const uint8_t* mac) {
    char key[13];
    buildRelayLabelPrefKey(mac, key, sizeof(key));
    Preferences prefs;
    prefs.begin("gwrelay", false);
    prefs.remove(key);
    prefs.end();
}

static uint8_t findNodeByMac(const uint8_t* mac) {
    for (uint8_t i = 1; i < nextId; i++) {
        if (nodes[i].mac[0] == 0 && nodes[i].mac[1] == 0) continue; // empty slot
        if (memcmp(nodes[i].mac, mac, 6) == 0) return i;
    }
    return 0;
}

// Find an empty/recycled slot or allocate a new one
static uint8_t findFreeSlot() {
    for (uint8_t i = 1; i < nextId; i++) {
        if (nodes[i].mac[0] == 0 && nodes[i].mac[1] == 0) return i;
    }
    if (nextId > MESH_MAX_NODES) return 0;
    return nextId++;
}

static uint8_t peekFreeSlot() {
    uint8_t slot = 0;
    if (xSemaphoreTake(nodesMutex, pdMS_TO_TICKS(50)) == pdTRUE) {
        for (uint8_t i = 1; i < nextId; i++) {
            if (nodes[i].mac[0] == 0 && nodes[i].mac[1] == 0) {
                slot = i;
                break;
            }
        }
        if (slot == 0 && nextId <= MESH_MAX_NODES) slot = nextId;
        xSemaphoreGive(nodesMutex);
    }
    return slot;
}

static uint8_t countRegisteredNodes() {
    uint8_t count = 0;
    if (xSemaphoreTake(nodesMutex, pdMS_TO_TICKS(50)) == pdTRUE) {
        for (uint8_t i = 1; i < nextId; i++) {
            if (nodes[i].mac[0] == 0 && nodes[i].mac[1] == 0) continue;
            count++;
        }
        xSemaphoreGive(nodesMutex);
    }
    return count;
}

static String buildPairCapacityFullJson(const char* macStr = nullptr) {
    JsonDocument doc;
    doc["type"] = "pair_capacity_full";
    doc["current_nodes"] = countRegisteredNodes();
    doc["max_nodes"] = MESH_MAX_NODES;
    if (macStr && *macStr) doc["mac"] = macStr;

    String out;
    serializeJson(doc, out);
    return out;
}

static uint32_t defaultCapabilitiesForType(NodeType type) {
    switch (type) {
        case NODE_SENSOR: return NODE_CAP_SENSOR_DATA;
        case NODE_ACTUATOR: return NODE_CAP_ACTUATORS;
        case NODE_HYBRID: return NODE_CAP_ACTUATORS;
        default: return 0;
    }
}

static uint8_t defaultActuatorCountForNode(const NodeRecord& node) {
    if (node.actuatorCount > 0) return node.actuatorCount;
    if (node.capabilities & NODE_CAP_ACTUATORS) return 4;
    return 0;
}

static bool nodeSupportsCapability(const NodeRecord& node, uint32_t capability) {
    return (node.capabilities & capability) != 0;
}

// *****************************************************************************
//  Web Auth helpers
// *****************************************************************************
static bool credentialsSet() {
    return webUsername[0] != '\0' && webPassHash[0] != '\0';
}

static void performGatewayFactoryReset(const char* sourceLabel);
static void clearStoredRouterCredentials();
static void saveGatewayForceSetupFlag(bool enabled);
static void disconnectAllNodesForFactoryReset();
static void mqttCleanupForFactoryReset();

static bool isWsAuthenticated(uint32_t clientId) {
    if (!credentialsSet()) return true;
    return authWsClients.count(clientId) > 0;
}

static void computeSha256Hex(const char* input, char* hexOut64) {
    uint8_t hash[32];
    mbedtls_sha256_context ctx;
    mbedtls_sha256_init(&ctx);
    mbedtls_sha256_starts(&ctx, 0);   // 0 = SHA-256 (not SHA-224)
    mbedtls_sha256_update(&ctx, (const unsigned char*)input, strlen(input));
    mbedtls_sha256_finish(&ctx, hash);
    mbedtls_sha256_free(&ctx);
    for (int i = 0; i < 32; i++) snprintf(hexOut64 + i * 2, 3, "%02x", hash[i]);
    hexOut64[64] = '\0';
}

static void generateHexToken(char* out, int byteCount) {
    // out must be at least byteCount*2 + 1 bytes
    for (int i = 0; i < byteCount; i++)
        snprintf(out + i * 2, 3, "%02x", (uint8_t)(esp_random() & 0xFF));
    out[byteCount * 2] = '\0';
}

static void loadWebCredentials() {
    Preferences prefs;
    prefs.begin("gwauth", true);   // read-only
    String u = prefs.getString("username", "");
    String h = prefs.getString("passhash", "");
    String t = prefs.getString("remtoken", "");
    prefs.end();
    strncpy(webUsername,   u.c_str(), 32); webUsername[32]   = '\0';
    strncpy(webPassHash,   h.c_str(), 64); webPassHash[64]   = '\0';
    strncpy(rememberToken, t.c_str(), 64); rememberToken[64] = '\0';
    Serial.printf("[AUTH]  Web credentials %s\n",
                  credentialsSet() ? "loaded" : "not set (open access)");
}

// Saves new username + pre-hashed password; also generates a fresh remember token.
static void saveWebCredentials(const char* user, const char* passHash) {
    generateHexToken(rememberToken, 32);
    Preferences prefs;
    prefs.begin("gwauth", false);  // read-write
    prefs.putString("username", user);
    prefs.putString("passhash", passHash);
    prefs.putString("remtoken", rememberToken);
    prefs.end();
    strncpy(webUsername, user,     32); webUsername[32] = '\0';
    strncpy(webPassHash, passHash, 64); webPassHash[64] = '\0';
    Serial.printf("[AUTH]  Web credentials saved for user \"%s\"\n", user);
}

// Parses the raw "Cookie" header and returns the value for the named cookie,
// or an empty String if not found. ESPAsyncWebServer v3 has no dedicated
// cookie API — cookies live in the plain HTTP header.
static String getCookieValue(AsyncWebServerRequest* req, const char* name) {
    const AsyncWebHeader* hdr = req->getHeader("Cookie");
    if (!hdr) return String();
    const String& raw = hdr->value();
    // raw looks like: "key1=val1; key2=val2; key3=val3"
    String nameEq = String(name) + "=";
    int start = 0;
    while (start < (int)raw.length()) {
        // Skip leading spaces
        while (start < (int)raw.length() && raw[start] == ' ') start++;
        int semi = raw.indexOf(';', start);
        String pair = (semi < 0) ? raw.substring(start) : raw.substring(start, semi);
        pair.trim();
        if (pair.startsWith(nameEq)) {
            return pair.substring(nameEq.length());
        }
        if (semi < 0) break;
        start = semi + 1;
    }
    // For Debugging: print the cookie parsing attempt to the Serial console
    Serial.printf("[AUTH]  Cookie \"%s\" not found in header: %s\n", name, raw.c_str());
    return String();
}

static bool shouldLogHttpAuthSuccess(AsyncWebServerRequest* req) {
    return req &&
        req->url() != "/api/gateway/ota" &&
        req->url() != "/api/node/ota";
}

// Returns true if the HTTP request carries a valid session or remember cookie.
static bool isHttpAuthenticated(AsyncWebServerRequest* req) {
    if (!credentialsSet()) {
        // For Debugging: print the authentication attempt to the Serial console
        if (shouldLogHttpAuthSuccess(req)) {
            Serial.printf("[AUTH]  HTTP auth not required for request to %s\n", req->url().c_str());
        }
        return true;
    }
    if (strlen(sessionToken) > 0) {
        String v = getCookieValue(req, "gwsession");
        if (v.length() > 0 && v.equals(sessionToken)) {
            // For Debugging: print the authentication attempt to the Serial console
            if (shouldLogHttpAuthSuccess(req)) {
                Serial.printf("[AUTH]  HTTP auth OK for request to %s\n", req->url().c_str());
            }
            return true;
        }
    }
    if (strlen(rememberToken) > 0) {
        String v = getCookieValue(req, "gwremember");
        if (v.length() > 0 && v.equals(rememberToken)) {
            // For Debugging: print the authentication attempt to the Serial console
            if (shouldLogHttpAuthSuccess(req)) {
                Serial.printf("[AUTH]  HTTP auth OK for request to %s\n", req->url().c_str());
            }
            return true;
        }
    }
    const AsyncWebHeader* tokenHdr = req->getHeader("X-GW-Token");
    if (tokenHdr) {
        const String token = tokenHdr->value();
        if ((strlen(sessionToken) > 0 && token.equals(sessionToken)) ||
            (strlen(rememberToken) > 0 && token.equals(rememberToken))) {
            if (shouldLogHttpAuthSuccess(req)) {
                Serial.printf("[AUTH]  HTTP token auth OK for request to %s\n", req->url().c_str());
            }
            return true;
        }
    }
    // For Debugging: print the authentication attempt to the Serial console
    Serial.printf("[AUTH]  HTTP auth failed for request to %s\n", req->url().c_str());
    return false;
}

// Broadcast a message only to authenticated WS clients
// (or to all clients when no credentials are configured).
static void wsBroadcast(const String& msg) {
    if (!credentialsSet()) { ws.textAll(msg); return; }
    for (uint32_t id : authWsClients) {
        AsyncWebSocketClient* c = ws.client(id);
        if (c && c->canSend()) c->text(msg);
        // For Debugging: print the message being sent to the Serial console
        Serial.printf("[WS]    Sent message to client %d: %s\n", id, msg.c_str());
    }
}

static size_t getGatewayOtaSlotSize() {
    const esp_partition_t* part = esp_ota_get_next_update_partition(nullptr);
    return part ? part->size : 0;
}

static bool gatewayOtaSupported() {
    return getGatewayOtaSlotSize() > 0;
}

static void setOtaError(GatewayOtaRequestState* state, const String& msg) {
    if (!state || state->error[0] != '\0') return;
    strncpy(state->error, msg.c_str(), sizeof(state->error) - 1);
    state->error[sizeof(state->error) - 1] = '\0';
    Serial.printf("[OTA]  ERROR: %s\n", state->error);
}

static void scanGatewayFirmwareMarkers(GatewayOtaRequestState* state,
                                       const uint8_t* data,
                                       size_t len) {
    if (!state || !data || len == 0) return;

    for (size_t i = 0; i < len; i++) {
        const char ch = (char)data[i];

        if (state->markerReadingVersion) {
            if (ch == '\0') {
                if (state->markerVersionLen > 0) {
                    state->incomingDisplayVersion[state->markerVersionLen] = '\0';
                }
                state->markerReadingVersion = false;
                state->markerVersionLen = 0;
                state->markerMatchIndex = 0;
                continue;
            }

            if (ch >= 32 && ch <= 126 && state->markerVersionLen < (OTA_FW_VERSION_MAX_LEN - 1)) {
                state->incomingDisplayVersion[state->markerVersionLen++] = ch;
                continue;
            }

            state->markerReadingVersion = false;
            state->markerVersionLen = 0;
            state->markerMatchIndex = 0;
        }

        if (state->hwMarkerReading) {
            if (ch == '\0') {
                if (state->hwMarkerLen > 0) {
                    state->incomingHwConfigId[state->hwMarkerLen] = '\0';
                }
                state->hwMarkerReading = false;
                state->hwMarkerLen = 0;
                state->hwMarkerMatchIndex = 0;
                continue;
            }

            if (ch >= 32 && ch <= 126 && state->hwMarkerLen < (OTA_HWCFG_ID_MAX_LEN - 1)) {
                state->incomingHwConfigId[state->hwMarkerLen++] = ch;
                continue;
            }

            state->hwMarkerReading = false;
            state->hwMarkerLen = 0;
            state->hwMarkerMatchIndex = 0;
        }

        if (ch == OTA_FW_MARKER[state->markerMatchIndex]) {
            state->markerMatchIndex++;
            if (state->markerMatchIndex == OTA_FW_MARKER_LEN) {
                state->markerReadingVersion = true;
                state->markerVersionLen = 0;
                memset(state->incomingDisplayVersion, 0, sizeof(state->incomingDisplayVersion));
                state->markerMatchIndex = 0;
            }
        } else {
            state->markerMatchIndex = (ch == OTA_FW_MARKER[0]) ? 1 : 0;
        }

        if (ch == OTA_HWCFG_MARKER[state->hwMarkerMatchIndex]) {
            state->hwMarkerMatchIndex++;
            if (state->hwMarkerMatchIndex == OTA_HWCFG_MARKER_LEN) {
                state->hwMarkerReading = true;
                state->hwMarkerLen = 0;
                memset(state->incomingHwConfigId, 0, sizeof(state->incomingHwConfigId));
                state->hwMarkerMatchIndex = 0;
            }
        } else {
            state->hwMarkerMatchIndex = (ch == OTA_HWCFG_MARKER[0]) ? 1 : 0;
        }
    }
}

static const char* getIncomingGatewayFirmwareVersion(const GatewayOtaRequestState* state) {
    if (!state) return "(unknown)";
    if (state->incomingDisplayVersion[0] != '\0') return state->incomingDisplayVersion;
    if (state->incomingVersion[0] != '\0') return state->incomingVersion;
    return "(unknown)";
}

static bool parseHardwareConfigId(const char* text, uint32_t* outValue = nullptr) {
    if (!text) return false;
    while (*text != '\0' && isspace((unsigned char)*text)) text++;
    if (*text == '\0') return false;

    char* end = nullptr;
    unsigned long value = strtoul(text, &end, 0);
    if (end == text) return false;
    while (*end != '\0' && isspace((unsigned char)*end)) end++;
    if (*end != '\0') return false;

    if (outValue) *outValue = (uint32_t)value;
    return true;
}

static bool hardwareConfigIdsMatch(const char* lhs, const char* rhs) {
    uint32_t lhsValue = 0;
    uint32_t rhsValue = 0;
    return parseHardwareConfigId(lhs, &lhsValue) &&
           parseHardwareConfigId(rhs, &rhsValue) &&
           lhsValue == rhsValue;
}

static bool validateGatewayFirmwareDescriptor(GatewayOtaRequestState* state) {
    if (!state) return false;
    if (state->descBytes < OTA_DESC_BUF_LEN) return false;
    if (state->metadataValidated) return true;

    const esp_app_desc_t* incoming =
        reinterpret_cast<const esp_app_desc_t*>(state->descBuf
            + sizeof(esp_image_header_t)
            + sizeof(esp_image_segment_header_t));
    const esp_app_desc_t* running = esp_app_get_description();

    strncpy(state->incomingVersion, incoming->version, sizeof(state->incomingVersion) - 1);
    state->incomingVersion[sizeof(state->incomingVersion) - 1] = '\0';

    if (running &&
        running->project_name[0] != '\0' &&
        incoming->project_name[0] != '\0' &&
        strncmp(running->project_name, incoming->project_name, sizeof(running->project_name)) != 0) {
        setOtaError(state, String("Firmware project mismatch: expected \"")
            + running->project_name + "\", got \"" + incoming->project_name + "\".");
        return false;
    }

    state->metadataValidated = true;
    Serial.printf("[OTA]  Incoming firmware descriptor version: %s\n",
                  state->incomingVersion[0] ? state->incomingVersion : "(unknown)");
    return true;
}

static void setCoprocOtaUploadError(CoprocOtaUploadRequestState* state, const String& msg) {
    if (!state || state->error[0] != '\0') return;
    strncpy(state->error, msg.c_str(), sizeof(state->error) - 1);
    state->error[sizeof(state->error) - 1] = '\0';
    Serial.printf("[COPROC OTA]  ERROR: %s\n", state->error);
}

static void scanCoprocFirmwareMarkers(CoprocOtaUploadRequestState* state,
                                      const uint8_t* data,
                                      size_t len) {
    if (!state || !data || len == 0) return;

    for (size_t i = 0; i < len; i++) {
        const char ch = (char)data[i];

        if (state->versionMarkerReading) {
            if (ch == '\0') {
                if (state->versionMarkerLen > 0) {
                    state->incomingDisplayVersion[state->versionMarkerLen] = '\0';
                }
                state->versionMarkerReading = false;
                state->versionMarkerLen = 0;
            } else if (ch >= 32 && ch <= 126 &&
                       state->versionMarkerLen < (COPROC_OTA_VERSION_MAX_LEN - 1)) {
                state->incomingDisplayVersion[state->versionMarkerLen++] = ch;
            } else {
                state->versionMarkerReading = false;
                state->versionMarkerLen = 0;
            }
        }

        if (state->hwMarkerReading) {
            if (ch == '\0') {
                if (state->hwMarkerLen > 0) {
                    state->incomingHwConfigId[state->hwMarkerLen] = '\0';
                }
                state->hwMarkerReading = false;
                state->hwMarkerLen = 0;
            } else if (ch >= 32 && ch <= 126 &&
                       state->hwMarkerLen < (HW_CONFIG_ID_LEN - 1)) {
                state->incomingHwConfigId[state->hwMarkerLen++] = ch;
            } else {
                state->hwMarkerReading = false;
                state->hwMarkerLen = 0;
            }
        }

        if (!state->versionMarkerReading) {
            if (ch == COPROC_OTA_FW_MARKER[state->versionMarkerMatchIndex]) {
                state->versionMarkerMatchIndex++;
                if (state->versionMarkerMatchIndex == COPROC_OTA_FW_MARKER_LEN) {
                    state->versionMarkerReading = true;
                    state->versionMarkerLen = 0;
                    memset(state->incomingDisplayVersion, 0, sizeof(state->incomingDisplayVersion));
                    state->versionMarkerMatchIndex = 0;
                }
            } else {
                state->versionMarkerMatchIndex = (ch == COPROC_OTA_FW_MARKER[0]) ? 1 : 0;
            }
        }

        if (!state->hwMarkerReading) {
            if (ch == COPROC_OTA_HWCFG_MARKER[state->hwMarkerMatchIndex]) {
                state->hwMarkerMatchIndex++;
                if (state->hwMarkerMatchIndex == COPROC_OTA_HWCFG_MARKER_LEN) {
                    state->hwMarkerReading = true;
                    state->hwMarkerLen = 0;
                    memset(state->incomingHwConfigId, 0, sizeof(state->incomingHwConfigId));
                    state->hwMarkerMatchIndex = 0;
                }
            } else {
                state->hwMarkerMatchIndex = (ch == COPROC_OTA_HWCFG_MARKER[0]) ? 1 : 0;
            }
        }
    }
}

static bool validateCoprocFirmwareDescriptor(CoprocOtaUploadRequestState* state) {
    if (!state) return false;
    if (state->descBytes < OTA_DESC_BUF_LEN) return false;
    if (state->metadataValidated) return true;

    const esp_app_desc_t* incoming =
        reinterpret_cast<const esp_app_desc_t*>(state->descBuf
            + sizeof(esp_image_header_t)
            + sizeof(esp_image_segment_header_t));

    strncpy(state->incomingVersion, incoming->version, sizeof(state->incomingVersion) - 1);
    state->incomingVersion[sizeof(state->incomingVersion) - 1] = '\0';
    strncpy(state->incomingProjectName, incoming->project_name, sizeof(state->incomingProjectName) - 1);
    state->incomingProjectName[sizeof(state->incomingProjectName) - 1] = '\0';

    if (coprocProjectName[0] != '\0' &&
        incoming->project_name[0] != '\0' &&
        strncmp(coprocProjectName, incoming->project_name, sizeof(incoming->project_name)) != 0) {
        setCoprocOtaUploadError(state, String("Coprocessor firmware project mismatch: expected \"")
            + coprocProjectName + "\", got \"" + incoming->project_name + "\".");
        return false;
    }

    state->metadataValidated = true;
    Serial.printf("[COPROC OTA]  Incoming coprocessor descriptor version: %s\n",
                  state->incomingVersion[0] ? state->incomingVersion : "(unknown)");
    return true;
}

static bool requestTargetsCoproc(AsyncWebServerRequest* req) {
    if (!req) return false;
    const AsyncWebHeader* hdr = req->getHeader("X-Target-MCU");
    return hdr && hdr->value().equalsIgnoreCase("coprocessor");
}

static void handleCoprocOtaUpload(AsyncWebServerRequest* req,
                                  const String& filename,
                                  size_t index,
                                  uint8_t* data,
                                  size_t len,
                                  bool final);
static bool isCoprocessorReservedForNodeOta();
static bool isCoprocessorReservedForCoprocOta();
static bool isOtaConflictError(const char* msg);

static void handleGatewayOtaUpload(AsyncWebServerRequest* req,
                                   const String& filename,
                                   size_t index,
                                   uint8_t* data,
                                   size_t len,
                                   bool final) {
    if (!isHttpAuthenticated(req)) return;
    if (requestTargetsCoproc(req)) {
        handleCoprocOtaUpload(req, filename, index, data, len, final);
        return;
    }

    auto* state = reinterpret_cast<GatewayOtaRequestState*>(req->_tempObject);
    if (index == 0) {
        if (state) {
            delete state;
            state = nullptr;
        }
        state = new GatewayOtaRequestState();
        req->_tempObject = state;
        state->started = true;
        const AsyncWebHeader* sizeHdr = req->getHeader("X-Firmware-Size");
        if (sizeHdr) {
            state->expectedSize = (size_t)strtoull(sizeHdr->value().c_str(), nullptr, 10);
        }
        strncpy(state->filename, filename.c_str(), sizeof(state->filename) - 1);
        state->filename[sizeof(state->filename) - 1] = '\0';

        if (isCoprocessorReservedForNodeOta() || isCoprocessorReservedForCoprocOta()) {
            setOtaError(state, COPROC_BUSY_MSG);
        } else if (otaUploadBusy) {
            setOtaError(state, "Another OTA upload is already in progress.");
        } else if (otaRebootPending) {
            setOtaError(state, "Gateway reboot pending. Wait for the device to come back online.");
        } else if (!gatewayOtaSupported()) {
            setOtaError(state, "This firmware layout does not support OTA updates.");
        } else {
            const size_t slotSize = getGatewayOtaSlotSize();
            if (state->expectedSize > 0 && state->expectedSize > slotSize) {
                setOtaError(state, String("Firmware image is too large for the OTA slot (")
                    + state->expectedSize + " > " + slotSize + " bytes).");
            } else if (!Update.begin(slotSize, U_FLASH)) {
                setOtaError(state, String("Could not start OTA: ") + Update.errorString());
            } else {
                otaUploadBusy = true;
                state->updateBegun = true;
                if (state->expectedSize > 0) {
                    Serial.printf("[OTA]  Upload started: \"%s\" (%u bytes)\n",
                                  state->filename[0] ? state->filename : "(unnamed)",
                                  (unsigned)state->expectedSize);
                } else {
                    Serial.printf("[OTA]  Upload started: \"%s\" (size unknown)\n",
                                  state->filename[0] ? state->filename : "(unnamed)");
                }
            }
        }
    }

    if (!state) return;

    if (state->error[0] != '\0') {
        if (final && state->updateBegun) {
            Update.abort();
            state->updateBegun = false;
        }
        return;
    }

    if (len > 0) {
        scanGatewayFirmwareMarkers(state, data, len);

        if (index == 0 && data[0] != ESP_IMAGE_HEADER_MAGIC) {
            setOtaError(state, "Uploaded file is not a valid ESP32 application image.");
        }

        if (state->error[0] == '\0' && !state->metadataValidated) {
            const size_t copyLen = std::min<size_t>(len, OTA_DESC_BUF_LEN - state->descBytes);
            memcpy(state->descBuf + state->descBytes, data, copyLen);
            state->descBytes += copyLen;

            if (state->descBytes >= OTA_DESC_BUF_LEN) {
                validateGatewayFirmwareDescriptor(state);
                if (state->error[0] != '\0' && state->updateBegun) {
                    Update.abort();
                    state->updateBegun = false;
                } else if (!state->descFlushed) {
                    size_t flushed = Update.write(state->descBuf, OTA_DESC_BUF_LEN);
                    if (flushed != OTA_DESC_BUF_LEN) {
                        setOtaError(state, String("Write failed: ") + Update.errorString());
                        if (state->updateBegun) {
                            Update.abort();
                            state->updateBegun = false;
                        }
                    } else {
                        state->written += flushed;
                        state->descFlushed = true;
                    }
                }
            }

            if (state->error[0] == '\0' && state->metadataValidated) {
                const size_t trailingLen = len - copyLen;
                if (trailingLen > 0) {
                    size_t flushed = Update.write(data + copyLen, trailingLen);
                    if (flushed != trailingLen) {
                        setOtaError(state, String("Write failed: ") + Update.errorString());
                        if (state->updateBegun) {
                            Update.abort();
                            state->updateBegun = false;
                        }
                    } else {
                        state->written += flushed;
                    }
                }
            }
        } else if (state->error[0] == '\0') {
            size_t written = Update.write(data, len);
            if (written != len) {
                setOtaError(state, String("Write failed: ") + Update.errorString());
                if (state->updateBegun) {
                    Update.abort();
                    state->updateBegun = false;
                }
            } else {
                state->written += written;
            }
        }
    }

    if (final && state->error[0] == '\0') {
        if (state->incomingDisplayVersion[0] == '\0' && state->incomingVersion[0] != '\0') {
            strncpy(state->incomingDisplayVersion, state->incomingVersion, sizeof(state->incomingDisplayVersion) - 1);
            state->incomingDisplayVersion[sizeof(state->incomingDisplayVersion) - 1] = '\0';
        }

        if (!state->metadataValidated) {
            setOtaError(state, "Firmware metadata could not be validated.");
        } else if (state->incomingHwConfigId[0] == '\0') {
            setOtaError(state, "Gateway firmware hardware configuration marker (GWHWCFG) is missing. Rebuild the uploaded gateway firmware with the current OTA markers.");
        } else if (!hardwareConfigIdsMatch(state->incomingHwConfigId, HW_CONFIG_ID)) {
            setOtaError(state, String("Gateway hardware configuration mismatch. This gateway expects hardware config ID ")
                + HW_CONFIG_ID + " but the uploaded firmware hardware config ID is "
                + state->incomingHwConfigId + ".");
        } else if (state->expectedSize > 0 && state->written != state->expectedSize) {
            setOtaError(state, String("Upload size mismatch: wrote ")
                + state->written + " of " + state->expectedSize + " bytes.");
        } else if (state->written == 0) {
            setOtaError(state, "Empty firmware upload received.");
        } else if (!Update.end(true)) {
            setOtaError(state, String("Firmware finalization failed: ") + Update.errorString());
        } else if (!Update.isFinished()) {
            setOtaError(state, "Firmware upload did not complete.");
        } else {
            state->ok = true;
            Serial.printf("[OTA]  Upload complete. Ready to reboot into version %s.\n",
                          getIncomingGatewayFirmwareVersion(state));
        }
    }

    if (final && !state->ok && state->updateBegun) {
        Update.abort();
        state->updateBegun = false;
    }
}

static uint32_t crc32Update(uint32_t crc, const uint8_t* data, size_t len) {
    crc = ~crc;
    while (len--) {
        crc ^= *data++;
        for (uint8_t i = 0; i < 8; i++) {
            crc = (crc >> 1) ^ (0xEDB88320u & (-(int32_t)(crc & 1u)));
        }
    }
    return ~crc;
}

static uint16_t crc16Ccitt(const uint8_t* data, size_t len) {
    uint16_t crc = 0xFFFF;
    for (size_t i = 0; i < len; i++) {
        crc ^= (uint16_t)data[i] << 8;
        for (uint8_t bit = 0; bit < 8; bit++) {
            crc = (crc & 0x8000) ? (uint16_t)((crc << 1) ^ 0x1021) : (uint16_t)(crc << 1);
        }
    }
    return crc;
}

static const char* nodeTypeToRole(NodeType type) {
    switch (type) {
        case NODE_SENSOR: return "SENSOR";
        case NODE_ACTUATOR: return "ACTUATOR";
        case NODE_HYBRID: return "HYBRID";
        default: return "UNKNOWN";
    }
}

static NodeType roleToNodeType(const char* role) {
    if (!role || role[0] == '\0') return (NodeType)0;
    if (strcmp(role, "SENSOR") == 0) return NODE_SENSOR;
    if (strcmp(role, "ACTUATOR") == 0) return NODE_ACTUATOR;
    if (strcmp(role, "HYBRID") == 0) return NODE_HYBRID;
    return (NodeType)0;
}

static bool handleNodeActuatorCommand(uint8_t nodeId, uint8_t actuatorId, uint8_t state,
                                      String* err = nullptr);
static bool handleNodeSettingCommand(uint8_t nodeId, uint8_t settingId, int16_t value,
                                     String* err = nullptr);
static bool handleNodeRebootCommand(uint8_t nodeId, String* err = nullptr);
static bool handleNodeUnpairCommand(uint8_t nodeId, String* err = nullptr);
static String buildNodesJson();
static String buildNodeSettingsJson(uint8_t nodeId);
static void disconnectNode(uint8_t nodeId);

static void mqttCopyString(char* dst, size_t dstSize, const String& value) {
    if (!dst || dstSize == 0) return;
    strncpy(dst, value.c_str(), dstSize - 1);
    dst[dstSize - 1] = '\0';
}

static String mqttTrimTopic(const String& value) {
    String out = value;
    out.trim();
    while (out.startsWith("/")) out.remove(0, 1);
    while (out.endsWith("/")) out.remove(out.length() - 1);
    return out;
}

static bool mqttIsPrintableAscii(const String& value, bool allowSpace = false) {
    if (value.isEmpty()) return false;
    for (size_t i = 0; i < value.length(); i++) {
        const unsigned char ch = (unsigned char)value[i];
        if (ch < 33 || ch > 126) {
            if (!(allowSpace && ch == ' ')) return false;
        }
    }
    return true;
}

static bool mqttHasConfiguredCredentials() {
    return mqttHost[0] != '\0' &&
           mqttBaseTopic[0] != '\0' &&
           mqttUsername[0] != '\0' &&
           mqttHasPassword &&
           mqttPassword[0] != '\0' &&
           mqttPort > 0;
}

static String mqttUnavailableReason() {
    if (!mqttEnabled) return "MQTT bridge is disabled.";
    if (!mqttHasConfiguredCredentials()) return "MQTT broker host, base topic, username, or password is missing.";
    if (gatewayNetworkMode != GATEWAY_ONLINE_STA) return "Gateway is not in router-connected mode.";
    if (WiFi.status() != WL_CONNECTED) return "Router Wi-Fi is disconnected.";
    return "";
}

static void mqttLogConfigSummary(const char* prefix) {
    Serial.printf("[MQTT] %s: enabled=%s host=\"%s\" port=%u base=\"%s\" user=\"%s\" password=%s\n",
                  prefix ? prefix : "Config",
                  mqttEnabled ? "yes" : "no",
                  mqttHost[0] ? mqttHost : "-",
                  mqttPort,
                  mqttBaseTopic[0] ? mqttBaseTopic : "-",
                  mqttUsername[0] ? mqttUsername : "-",
                  mqttHasPassword ? "stored" : "missing");
}

static void mqttSetLastError(const String& msg) {
    if (String(mqttLastError) == msg) return;
    mqttCopyString(mqttLastError, sizeof(mqttLastError), msg);
    if (mqttLastError[0] != '\0') {
        Serial.printf("[MQTT] Error: %s\n", mqttLastError);
    }
    mqttMetaDirty = true;
}

static void mqttClearLastError() {
    if (mqttLastError[0] == '\0') return;
    Serial.printf("[MQTT] Error cleared (previous: %s)\n", mqttLastError);
    mqttLastError[0] = '\0';
    mqttMetaDirty = true;
}

static uint32_t mqttNodeBit(uint8_t nodeId) {
    return (nodeId > 0 && nodeId < 32) ? (1UL << nodeId) : 0UL;
}

static uint32_t mqttSensorBit(uint8_t sensorId) {
    return (sensorId < 32) ? (1UL << sensorId) : 0UL;
}

static bool mqttIsNodeSensorStateHeld(uint8_t nodeId, uint8_t sensorId) {
    if (nodeId == 0 || nodeId > MESH_MAX_NODES) return false;
    return (mqttNodeHeldSensorStateMask[nodeId] & mqttSensorBit(sensorId)) != 0;
}

static void mqttHoldNodeSensorState(uint8_t nodeId, uint8_t sensorId) {
    if (nodeId == 0 || nodeId > MESH_MAX_NODES) return;
    mqttNodeHeldSensorStateMask[nodeId] |= mqttSensorBit(sensorId);
}

static void mqttReleaseNodeSensorState(uint8_t nodeId, uint8_t sensorId) {
    if (nodeId == 0 || nodeId > MESH_MAX_NODES) return;
    mqttNodeHeldSensorStateMask[nodeId] &= ~mqttSensorBit(sensorId);
}

static void mqttReleaseAllNodeSensorStates(uint8_t nodeId) {
    if (nodeId == 0 || nodeId > MESH_MAX_NODES) return;
    mqttNodeHeldSensorStateMask[nodeId] = 0;
}

static void mqttMarkNodeDiscoveryDirty(uint8_t nodeId) {
    mqttNodeDiscoveryDirtyMask |= mqttNodeBit(nodeId);
}

static void mqttMarkNodeSummaryDirty(uint8_t nodeId) {
    mqttNodeSummaryDirtyMask |= mqttNodeBit(nodeId);
}

static void mqttMarkNodeSensorStateDirty(uint8_t nodeId) {
    mqttNodeSensorStateDirtyMask |= mqttNodeBit(nodeId);
}

static void mqttMarkNodeActuatorStateDirty(uint8_t nodeId) {
    mqttNodeActuatorStateDirtyMask |= mqttNodeBit(nodeId);
}

static void mqttMarkNodeSettingsStateDirty(uint8_t nodeId) {
    mqttNodeSettingsStateDirtyMask |= mqttNodeBit(nodeId);
}

static void mqttMarkBuiltinDiscoveryDirty() {
    mqttBuiltinDiscoveryDirty = true;
}

static void mqttMarkBuiltinStateDirty() {
    mqttBuiltinStateDirty = true;
}

static void mqttMarkMetaDirty() {
    mqttMetaDirty = true;
}

static void mqttMarkAllDirty() {
    mqttRepublishAllPending = true;
    mqttGatewayControlDiscoveryDirty = true;
    mqttBuiltinDiscoveryDirty = true;
    mqttBuiltinStateDirty = true;
    mqttMetaDirty = true;
    mqttNodeDiscoveryDirtyMask = 0xFFFFFFFFUL;
    mqttNodeSummaryDirtyMask = 0xFFFFFFFFUL;
    mqttNodeSensorStateDirtyMask = 0xFFFFFFFFUL;
    mqttNodeActuatorStateDirtyMask = 0xFFFFFFFFUL;
    mqttNodeSettingsStateDirtyMask = 0xFFFFFFFFUL;
}

static void mqttMacToTopicId(const uint8_t* mac, char* out, size_t outLen) {
    if (!out || outLen < 13) return;
    snprintf(out, outLen, "%02x%02x%02x%02x%02x%02x",
             mac[0], mac[1], mac[2], mac[3], mac[4], mac[5]);
}

static void mqttStringToTopicId(const String& mac, char* out, size_t outLen) {
    if (!out || outLen < 13) return;
    size_t idx = 0;
    for (size_t i = 0; i < mac.length() && idx < 12; i++) {
        const char ch = mac[i];
        if (isxdigit((unsigned char)ch)) {
            out[idx++] = (char)tolower((unsigned char)ch);
        }
    }
    out[idx] = '\0';
}

static void mqttRefreshGatewayTopicId() {
    const String mac = WiFi.macAddress();
    if (mac.length() > 0) {
        mqttStringToTopicId(mac, mqttGatewayTopicId, sizeof(mqttGatewayTopicId));
    }
}

static String mqttGatewayRootTopic() {
    return String(mqttBaseTopic) + "/gateways/" + mqttGatewayTopicId;
}

static String mqttNodeBaseTopic(const char* nodeMacId) {
    return mqttGatewayRootTopic() + "/nodes/" + nodeMacId;
}

static bool mqttShouldBeConnected() {
    return mqttEnabled &&
           mqttHasConfiguredCredentials() &&
           gatewayNetworkMode == GATEWAY_ONLINE_STA &&
           WiFi.status() == WL_CONNECTED;
}

static void loadMqttConfig() {
    Preferences prefs;
    prefs.begin("gwconfig", true);
    const bool enabled = prefs.getBool("mqtt_en", false);
    const String host = prefs.getString("mqtt_host", "");
    const uint16_t port = prefs.getUShort("mqtt_port", MQTT_DEFAULT_PORT);
    const String baseTopic = prefs.getString("mqtt_base", "esp32/mesh");
    const String username = prefs.getString("mqtt_user", "");
    const String password = prefs.getString("mqtt_pass", "");
    prefs.end();

    mqttEnabled = enabled;
    mqttCopyString(mqttHost, sizeof(mqttHost), host);
    mqttPort = port ? port : MQTT_DEFAULT_PORT;
    mqttCopyString(mqttBaseTopic, sizeof(mqttBaseTopic), mqttTrimTopic(baseTopic));
    mqttCopyString(mqttUsername, sizeof(mqttUsername), username);
    mqttCopyString(mqttPassword, sizeof(mqttPassword), password);
    mqttHasPassword = mqttPassword[0] != '\0';

    if (mqttEnabled && !mqttHasConfiguredCredentials()) {
        mqttEnabled = false;
        mqttSetLastError("MQTT is disabled until broker host, base topic, username, and password are configured.");
    } else {
        mqttClearLastError();
    }
    mqttLogConfigSummary("Config loaded");
}

static void saveMqttConfig(bool enabled,
                           const String& host,
                           uint16_t port,
                           const String& baseTopic,
                           const String& username,
                           const String& password,
                           bool updatePassword) {
    const String trimmedBase = mqttTrimTopic(baseTopic);
    Preferences prefs;
    prefs.begin("gwconfig", false);
    prefs.putBool("mqtt_en", enabled);
    prefs.putString("mqtt_host", host);
    prefs.putUShort("mqtt_port", port);
    prefs.putString("mqtt_base", trimmedBase);
    prefs.putString("mqtt_user", username);
    if (updatePassword) prefs.putString("mqtt_pass", password);
    prefs.end();

    mqttEnabled = enabled;
    mqttCopyString(mqttHost, sizeof(mqttHost), host);
    mqttPort = port;
    mqttCopyString(mqttBaseTopic, sizeof(mqttBaseTopic), trimmedBase);
    mqttCopyString(mqttUsername, sizeof(mqttUsername), username);
    if (updatePassword) {
        mqttCopyString(mqttPassword, sizeof(mqttPassword), password);
        mqttHasPassword = mqttPassword[0] != '\0';
    }
    if (mqttEnabled && !mqttHasConfiguredCredentials()) {
        mqttEnabled = false;
        mqttSetLastError("MQTT is disabled until broker host, base topic, username, and password are configured.");
    } else {
        mqttClearLastError();
    }
    mqttMarkAllDirty();
    mqttLogConfigSummary("Config saved");
}

static bool mqttQueueRemovedNodeSnapshot(const NodeRecord& node) {
    for (uint8_t i = 0; i < MESH_MAX_NODES; i++) {
        if (!mqttRemovedNodes[i].active) {
            MqttRemovedNodeSnapshot& snapshot = mqttRemovedNodes[i];
            memset(&snapshot, 0, sizeof(snapshot));
            snapshot.active = true;
            mqttMacToTopicId(node.mac, snapshot.macId, sizeof(snapshot.macId));
            snapshot.hadSensors = nodeSupportsCapability(node, NODE_CAP_SENSOR_DATA);
            snapshot.sensorCount = node.sensorCount;
            for (uint8_t j = 0; j < node.sensorCount && j < NODE_MAX_SENSORS; j++) {
                snapshot.sensorIds[j] = node.sensorSchema[j].id;
            }
            snapshot.hadActuators = nodeSupportsCapability(node, NODE_CAP_ACTUATORS);
            snapshot.actuatorCount = defaultActuatorCountForNode(node);
            for (uint8_t j = 0; j < snapshot.actuatorCount && j < NODE_MAX_ACTUATORS; j++) {
                snapshot.actuatorIds[j] = (node.actuatorCount > j) ? node.actuatorSchema[j].id : j;
            }
            snapshot.settingsCount = node.settingsCount;
            for (uint8_t j = 0; j < node.settingsCount && j < NODE_MAX_SETTINGS; j++) {
                snapshot.settingIds[j] = node.settings[j].id;
                snapshot.settingTypes[j] = node.settings[j].type;
            }
            return true;
        }
    }
    return false;
}

static String mqttConnectStateString(int state) {
    switch (state) {
        case MQTT_CONNECTION_TIMEOUT: return "Connection timeout.";
        case MQTT_CONNECTION_LOST: return "Connection lost.";
        case MQTT_CONNECT_FAILED: return "Broker connect failed.";
        case MQTT_DISCONNECTED: return "Disconnected.";
        case MQTT_CONNECTED: return "Connected.";
        case MQTT_CONNECT_BAD_PROTOCOL: return "Unsupported MQTT protocol.";
        case MQTT_CONNECT_BAD_CLIENT_ID: return "Rejected: bad client ID.";
        case MQTT_CONNECT_UNAVAILABLE: return "Broker unavailable.";
        case MQTT_CONNECT_BAD_CREDENTIALS: return "Rejected: bad MQTT username or password.";
        case MQTT_CONNECT_UNAUTHORIZED: return "Rejected: unauthorized.";
        default: return String("MQTT error ") + String(state) + ".";
    }
}

static void mqttPublishPending(unsigned long now);
static void processMqtt(unsigned long now);
static void mqttOnMessage(char* topic, uint8_t* payload, unsigned int length);

static void setNodeOtaUploadError(NodeOtaUploadRequestState* state, const String& msg) {
    if (!state || state->error[0] != '\0') return;
    strncpy(state->error, msg.c_str(), sizeof(state->error) - 1);
    state->error[sizeof(state->error) - 1] = '\0';
    Serial.printf("[NODE OTA]  ERROR: %s\n", state->error);
}

static void scanNodeFirmwareMarkers(NodeOtaUploadRequestState* state,
                                    const uint8_t* data,
                                    size_t len) {
    if (!state || !data || len == 0) return;

    for (size_t i = 0; i < len; i++) {
        const char ch = (char)data[i];

        if (state->versionMarkerReading) {
            if (ch == '\0') {
                if (state->versionMarkerLen > 0) {
                    state->incomingDisplayVersion[state->versionMarkerLen] = '\0';
                }
                state->versionMarkerReading = false;
                state->versionMarkerLen = 0;
            } else if (ch >= 32 && ch <= 126 &&
                       state->versionMarkerLen < (NODE_OTA_VERSION_MAX_LEN - 1)) {
                state->incomingDisplayVersion[state->versionMarkerLen++] = ch;
            } else {
                state->versionMarkerReading = false;
                state->versionMarkerLen = 0;
            }
        }

        if (state->roleMarkerReading) {
            if (ch == '\0') {
                if (state->roleMarkerLen > 0) state->incomingRole[state->roleMarkerLen] = '\0';
                state->roleMarkerReading = false;
                state->roleMarkerLen = 0;
            } else if (ch >= 'A' && ch <= 'Z' &&
                       state->roleMarkerLen < (sizeof(state->incomingRole) - 1)) {
                state->incomingRole[state->roleMarkerLen++] = ch;
            } else {
                state->roleMarkerReading = false;
                state->roleMarkerLen = 0;
            }
        }

        if (state->hwMarkerReading) {
            if (ch == '\0') {
                if (state->hwMarkerLen > 0) state->incomingHwConfigId[state->hwMarkerLen] = '\0';
                state->hwMarkerReading = false;
                state->hwMarkerLen = 0;
            } else if (ch >= 32 && ch <= 126 &&
                       state->hwMarkerLen < (sizeof(state->incomingHwConfigId) - 1)) {
                state->incomingHwConfigId[state->hwMarkerLen++] = ch;
            } else {
                state->hwMarkerReading = false;
                state->hwMarkerLen = 0;
            }
        }

        if (!state->versionMarkerReading) {
            if (ch == NODE_OTA_FW_MARKER[state->versionMarkerMatchIndex]) {
                state->versionMarkerMatchIndex++;
                if (state->versionMarkerMatchIndex == NODE_OTA_FW_MARKER_LEN) {
                    state->versionMarkerReading = true;
                    state->versionMarkerLen = 0;
                    memset(state->incomingDisplayVersion, 0, sizeof(state->incomingDisplayVersion));
                    state->versionMarkerMatchIndex = 0;
                }
            } else {
                state->versionMarkerMatchIndex = (ch == NODE_OTA_FW_MARKER[0]) ? 1 : 0;
            }
        }

        if (!state->roleMarkerReading) {
            if (ch == NODE_OTA_ROLE_MARKER[state->roleMarkerMatchIndex]) {
                state->roleMarkerMatchIndex++;
                if (state->roleMarkerMatchIndex == NODE_OTA_ROLE_MARKER_LEN) {
                    state->roleMarkerReading = true;
                    state->roleMarkerLen = 0;
                    memset(state->incomingRole, 0, sizeof(state->incomingRole));
                    state->roleMarkerMatchIndex = 0;
                }
            } else {
                state->roleMarkerMatchIndex = (ch == NODE_OTA_ROLE_MARKER[0]) ? 1 : 0;
            }
        }

        if (!state->hwMarkerReading) {
            if (ch == NODE_OTA_HWCFG_MARKER[state->hwMarkerMatchIndex]) {
                state->hwMarkerMatchIndex++;
                if (state->hwMarkerMatchIndex == NODE_OTA_HWCFG_MARKER_LEN) {
                    state->hwMarkerReading = true;
                    state->hwMarkerLen = 0;
                    memset(state->incomingHwConfigId, 0, sizeof(state->incomingHwConfigId));
                    state->hwMarkerMatchIndex = 0;
                }
            } else {
                state->hwMarkerMatchIndex = (ch == NODE_OTA_HWCFG_MARKER[0]) ? 1 : 0;
            }
        }
    }
}

static String buildMetaJson();  // forward declaration

static void broadcastMetaIfClientsConnected() {
    if (ws.count() > 0) wsBroadcast(buildMetaJson());
}

static bool validateNodeFirmwareDescriptor(NodeOtaUploadRequestState* state) {
    if (!state) return false;
    if (state->descBytes < OTA_DESC_BUF_LEN) return false;
    if (state->metadataValidated) return true;

    const esp_app_desc_t* incoming =
        reinterpret_cast<const esp_app_desc_t*>(state->descBuf
            + sizeof(esp_image_header_t)
            + sizeof(esp_image_segment_header_t));

    strncpy(state->incomingVersion, incoming->version, sizeof(state->incomingVersion) - 1);
    state->incomingVersion[sizeof(state->incomingVersion) - 1] = '\0';
    state->metadataValidated = true;

    Serial.printf("[NODE OTA]  Incoming firmware descriptor version: %s\n",
                  state->incomingVersion[0] ? state->incomingVersion : "(unknown)");
    return true;
}

static String buildNodeOtaJson() {
    JsonDocument doc;
    doc["type"] = "node_ota_state";
    doc["active"] = nodeOtaJob.active;
    doc["helper_online"] = coprocOnline;
    doc["upload_busy"] = nodeOtaJob.uploadBusy;
    doc["node_id"] = nodeOtaJob.nodeId;
    doc["stage"] = (int)nodeOtaJob.stage;
    doc["progress"] = nodeOtaJob.progress;
    doc["message"] = nodeOtaJob.message;
    doc["error"] = nodeOtaJob.error;
    doc["version"] = nodeOtaJob.version;
    if (nodeOtaJob.nodeId > 0 && nodeOtaJob.nodeId < nextId) {
        doc["node_name"] = nodes[nodeOtaJob.nodeId].name;
        doc["node_mac"] = macToStr(nodes[nodeOtaJob.nodeId].mac);
    }
    String out;
    serializeJson(doc, out);
    return out;
}

static void broadcastNodeOtaState() {
    wsBroadcast(buildNodeOtaJson());
}

static String buildCoprocOtaJson() {
    JsonDocument doc;
    doc["type"] = "coproc_ota_state";
    doc["active"] = coprocOtaJob.active;
    doc["online"] = coprocOnline;
    doc["upload_busy"] = coprocOtaJob.uploadBusy;
    doc["stage"] = (int)coprocOtaJob.stage;
    doc["progress"] = coprocOtaJob.progress;
    doc["message"] = coprocOtaJob.message;
    doc["error"] = coprocOtaJob.error;
    doc["version"] = coprocOtaJob.version;
    doc["current_version"] = coprocFwVersion;
    String out;
    serializeJson(doc, out);
    return out;
}

static void broadcastCoprocOtaState() {
    wsBroadcast(buildCoprocOtaJson());
}

static void clearNodeOtaJob(bool removeFile = true) {
    if (nodeOtaJob.file) nodeOtaJob.file.close();
    if (removeFile && LittleFS.exists(NODE_OTA_FILE_PATH)) {
        LittleFS.remove(NODE_OTA_FILE_PATH);
    }
    nodeOtaJob = NodeOtaJobState{};
    broadcastNodeOtaState();
}

static void clearCoprocOtaJob(bool removeFile = true) {
    if (coprocOtaJob.file) coprocOtaJob.file.close();
    if (removeFile && LittleFS.exists(COPROC_OTA_FILE_PATH)) {
        LittleFS.remove(COPROC_OTA_FILE_PATH);
    }
    coprocOtaJob = CoprocOtaJobState{};
    broadcastCoprocOtaState();
}

static void setCoprocOtaJobMessage(const String& msg, uint8_t progress = 0) {
    coprocOtaJob.lastActivityAt = millis();
    const bool messageChanged = strncmp(coprocOtaJob.message, msg.c_str(), sizeof(coprocOtaJob.message)) != 0;
    const bool progressChanged = coprocOtaJob.progress != progress;
    if (messageChanged) {
        strncpy(coprocOtaJob.message, msg.c_str(), sizeof(coprocOtaJob.message) - 1);
        coprocOtaJob.message[sizeof(coprocOtaJob.message) - 1] = '\0';
        Serial.printf("[COPROC OTA]  %s\n", coprocOtaJob.message);
    }
    if (messageChanged || progressChanged) {
        coprocOtaJob.progress = progress;
        coprocOtaJob.stageStartedAt = millis();
        broadcastCoprocOtaState();
    }
}

static void setCoprocOtaJobError(const String& msg) {
    coprocOtaJob.stage = COPROC_OTA_JOB_ERROR;
    coprocOtaJob.awaitingAck = false;
    coprocOtaJob.awaitingFrameType = 0;
    if (strncmp(coprocOtaJob.error, msg.c_str(), sizeof(coprocOtaJob.error)) != 0) {
        strncpy(coprocOtaJob.error, msg.c_str(), sizeof(coprocOtaJob.error) - 1);
        coprocOtaJob.error[sizeof(coprocOtaJob.error) - 1] = '\0';
    }
    setCoprocOtaJobMessage(msg, coprocOtaJob.progress);
}

static void setCoprocOtaJobSuccess(const String& msg) {
    coprocOtaJob.stage = COPROC_OTA_JOB_SUCCESS;
    coprocOtaJob.awaitingAck = false;
    coprocOtaJob.awaitingFrameType = 0;
    coprocOtaJob.error[0] = '\0';
    setCoprocOtaJobMessage(msg, 100);
}

static bool isCoprocessorReservedForNodeOta() {
    return nodeOtaJob.active || nodeOtaJob.uploadBusy;
}

static bool isCoprocessorReservedForCoprocOta() {
    return coprocOtaJob.active || coprocOtaJob.uploadBusy;
}

static bool isOtaConflictError(const char* msg) {
    return strcmp(msg, "Another OTA upload is already in progress.") == 0 ||
           strcmp(msg, COPROC_BUSY_MSG) == 0;
}

static void setNodeOtaJobMessage(const String& msg, uint8_t progress = 0) {
    nodeOtaJob.lastActivityAt = millis();
    const bool messageChanged = strncmp(nodeOtaJob.message, msg.c_str(), sizeof(nodeOtaJob.message)) != 0;
    const bool progressChanged = nodeOtaJob.progress != progress;
    if (messageChanged) {
        strncpy(nodeOtaJob.message, msg.c_str(), sizeof(nodeOtaJob.message) - 1);
        nodeOtaJob.message[sizeof(nodeOtaJob.message) - 1] = '\0';
        Serial.printf("[NODE OTA]  %s\n", nodeOtaJob.message);
    }
    if (messageChanged || progressChanged) {
        nodeOtaJob.progress = progress;
        nodeOtaJob.stageStartedAt = millis();
        broadcastNodeOtaState();
    }
}

static void setNodeOtaJobError(const String& msg) {
    nodeOtaJob.stage = NODE_OTA_JOB_ERROR;
    nodeOtaJob.awaitingAck = false;
    nodeOtaJob.awaitingFrameType = 0;
    if (strncmp(nodeOtaJob.error, msg.c_str(), sizeof(nodeOtaJob.error)) != 0) {
        strncpy(nodeOtaJob.error, msg.c_str(), sizeof(nodeOtaJob.error) - 1);
        nodeOtaJob.error[sizeof(nodeOtaJob.error) - 1] = '\0';
    }
    setNodeOtaJobMessage(msg, nodeOtaJob.progress);
}

static bool isRecoverableNodeOtaTimeout() {
    return nodeOtaJob.stage == NODE_OTA_JOB_ERROR &&
           strncmp(nodeOtaJob.error, "Node OTA timed out.", sizeof(nodeOtaJob.error)) == 0;
}

static void randomAscii(char* out, size_t len, const char* alphabet) {
    if (!out || len == 0) return;
    const size_t alphaLen = strlen(alphabet);
    if (alphaLen == 0) {
        out[0] = '\0';
        return;
    }
    for (size_t i = 0; i + 1 < len; i++) {
        out[i] = alphabet[esp_random() % alphaLen];
    }
    out[len - 1] = '\0';
}

static void buildNodeOtaCredentials() {
    const char* alnum = "ABCDEFGHJKLMNPQRSTUVWXYZ23456789";
    snprintf(nodeOtaJob.apSsid, sizeof(nodeOtaJob.apSsid), "NodeOTA-%02X%02X",
             (unsigned)(nodeOtaJob.sessionId >> 8) & 0xFF,
             (unsigned)(nodeOtaJob.sessionId) & 0xFF);
    randomAscii(nodeOtaJob.apPassword, sizeof(nodeOtaJob.apPassword), alnum);
}

static void requestCoprocReboot() {
    digitalWrite(COPROC_RESET_PIN, HIGH);
    delay(80);
    digitalWrite(COPROC_RESET_PIN, LOW);
    lastCoprocRecoveryPulseAt = millis();
    Serial.println("[C3]  Reboot pulse sent to coprocessor.");
}

static void resetCoprocRx() {
    coprocRx = CoprocRxState{};
}

static void resetCoprocAck() {
    coprocAck = CoprocAckState{};
}

static void flushCoprocSerialInput() {
    while (coprocSerial.available() > 0) {
        coprocSerial.read();
    }
    resetCoprocRx();
    resetCoprocAck();
}

static bool sendCoprocFrame(uint8_t type, const void* payload, size_t len) {
    if (len > COPROC_FRAME_MAX_PAYLOAD) return false;
    uint8_t headerBuf[sizeof(CoprocFrameHeader)];
    CoprocFrameHeader hdr{COPROC_FRAME_MAGIC, type, (uint16_t)len};
    memcpy(headerBuf, &hdr, sizeof(hdr));

    uint8_t crcBuf[2];
    uint8_t crcData[1 + 2 + COPROC_FRAME_MAX_PAYLOAD] = {0};
    crcData[0] = type;
    crcData[1] = (uint8_t)(len & 0xFF);
    crcData[2] = (uint8_t)((len >> 8) & 0xFF);
    if (len > 0 && payload) memcpy(crcData + 3, payload, len);
    uint16_t crc = crc16Ccitt(crcData, len + 3);
    crcBuf[0] = (uint8_t)(crc & 0xFF);
    crcBuf[1] = (uint8_t)((crc >> 8) & 0xFF);

    size_t written = coprocSerial.write(headerBuf, sizeof(headerBuf));
    if (len > 0 && payload) written += coprocSerial.write((const uint8_t*)payload, len);
    written += coprocSerial.write(crcBuf, sizeof(crcBuf));
    coprocSerial.flush();
    return written == (sizeof(headerBuf) + len + sizeof(crcBuf));
}

static void handleCoprocFrame(uint8_t type, const uint8_t* payload, size_t len) {
    if (type == COPROC_FRAME_ACK) {
        if (len < sizeof(CoprocAckPayload)) return;
        const auto* ack = reinterpret_cast<const CoprocAckPayload*>(payload);
        const unsigned long now = millis();
        const bool linkJobWaiting =
            (nodeOtaJob.active && nodeOtaJob.awaitingAck) ||
            (coprocOtaJob.active && coprocOtaJob.awaitingAck);
        const bool ignoreHelloAck =
            linkJobWaiting &&
            ack->original_type == COPROC_FRAME_HELLO &&
            ((nodeOtaJob.active && nodeOtaJob.awaitingFrameType != COPROC_FRAME_HELLO) ||
             (coprocOtaJob.active && coprocOtaJob.awaitingFrameType != COPROC_FRAME_HELLO));
        if (ignoreHelloAck) {
            coprocOnline = ack->ok != 0;
            lastCoprocAckAt = now;
            return;
        }
        coprocAck.ready = true;
        coprocAck.originalType = ack->original_type;
        coprocAck.ok = ack->ok != 0;
        coprocAck.value = ack->value;
        memcpy(coprocAck.message, ack->message, sizeof(coprocAck.message));
        lastCoprocAckAt = now;
        if (nodeOtaJob.active) nodeOtaJob.lastAckAt = now;
        if (coprocOtaJob.active) coprocOtaJob.lastAckAt = now;
        if (ack->original_type != COPROC_FRAME_UPLOAD_CHUNK) {
            Serial.printf("[C3]  ACK type=0x%02X ok=%u value=%lu msg=\"%s\"\n",
                          ack->original_type,
                          ack->ok,
                          (unsigned long)ack->value,
                          ack->message);
        }
        return;
    }

    if (type == COPROC_FRAME_INFO) {
        if (len < sizeof(CoprocInfoPayload)) return;
        const auto* info = reinterpret_cast<const CoprocInfoPayload*>(payload);
        coprocOnline = true;
        lastCoprocAckAt = millis();
        coprocOtaSupportedRemote = info->ota_supported != 0;
        coprocOtaMaxBytes = info->ota_max_bytes;
        strncpy(coprocFwVersion, info->fw_version, sizeof(coprocFwVersion) - 1);
        coprocFwVersion[sizeof(coprocFwVersion) - 1] = '\0';
        strncpy(coprocHwConfigId, info->hw_config_id, sizeof(coprocHwConfigId) - 1);
        coprocHwConfigId[sizeof(coprocHwConfigId) - 1] = '\0';
        strncpy(coprocProjectName, info->project_name, sizeof(coprocProjectName) - 1);
        coprocProjectName[sizeof(coprocProjectName) - 1] = '\0';
        Serial.printf("[C3]  INFO version=%s hw=%s ota=%u slot=%lu project=\"%s\"\n",
                      coprocFwVersion[0] ? coprocFwVersion : "(unknown)",
                      coprocHwConfigId[0] ? coprocHwConfigId : "(unknown)",
                      (unsigned)info->ota_supported,
                      (unsigned long)coprocOtaMaxBytes,
                      coprocProjectName[0] ? coprocProjectName : "(unknown)");
        if (coprocOtaJob.active && coprocOtaJob.stage == COPROC_OTA_JOB_WAIT_REBOOT) {
            const bool versionMatches =
                coprocOtaJob.version[0] != '\0' &&
                coprocFwVersion[0] != '\0' &&
                strncmp(coprocOtaJob.version, coprocFwVersion, sizeof(coprocOtaJob.version) - 1) == 0;
            if (versionMatches) {
                setCoprocOtaJobSuccess(String("Coprocessor reconnected with firmware v") + coprocFwVersion + ".");
            }
        }
        broadcastMetaIfClientsConnected();
        if (coprocOtaJob.active) broadcastCoprocOtaState();
        return;
    }

    if (type == COPROC_FRAME_STATUS) {
        if (len < sizeof(CoprocStatusPayload)) return;
        const auto* status = reinterpret_cast<const CoprocStatusPayload*>(payload);
        Serial.printf("[C3]  STATUS session=%lu phase=%u progress=%u err=%u msg=\"%s\"\n",
                      (unsigned long)status->session_id,
                      status->phase,
                      status->progress,
                      status->error_code,
                      status->message);
        if (nodeOtaJob.active && status->session_id == nodeOtaJob.sessionId) {
            bool recoveredFromTimeout = false;
            nodeOtaJob.lastActivityAt = millis();
            if (status->phase == COPROC_HELPER_AP_READY) nodeOtaJob.helperApReady = true;
            if (status->phase == COPROC_HELPER_DONE || status->phase == NODE_OTA_SUCCESS) {
                nodeOtaJob.helperTransferDone = true;
                if (nodeOtaJob.stage == NODE_OTA_JOB_ERROR &&
                    strncmp(nodeOtaJob.error, "Node OTA timed out.", sizeof(nodeOtaJob.error)) == 0) {
                    nodeOtaJob.stage = NODE_OTA_JOB_WAIT_REJOIN;
                    recoveredFromTimeout = true;
                }
            }
            if (status->phase == COPROC_HELPER_ERROR || status->phase == NODE_OTA_ERROR) {
                setNodeOtaJobError(status->message[0] ? status->message : "Coprocessor reported an OTA error.");
            } else if (recoveredFromTimeout) {
                setNodeOtaJobMessage("Firmware sent to node. Waiting for node to reconnect...", 95);
            } else {
                setNodeOtaJobMessage(status->message[0] ? status->message : "OTA helper status updated.",
                                     status->progress);
            }
            return;
        }

        if (coprocOtaJob.active && status->session_id == coprocOtaJob.sessionId) {
            coprocOtaJob.lastActivityAt = millis();
            if (status->phase == COPROC_HELPER_ERROR) {
                setCoprocOtaJobError(status->message[0] ? status->message : "Coprocessor reported an OTA error.");
            } else if (status->phase == COPROC_HELPER_DONE) {
                coprocOtaJob.flashReportedDone = true;
                coprocOtaJob.stage = COPROC_OTA_JOB_WAIT_REBOOT;
                coprocOnline = false;
                setCoprocOtaJobMessage(status->message[0] ? status->message : "Firmware flashed. Waiting for coprocessor reboot...",
                                       status->progress ? status->progress : 95);
            } else {
                setCoprocOtaJobMessage(status->message[0] ? status->message : "Coprocessor OTA status updated.",
                                       status->progress);
            }
        }
    }
}

static void processCoprocSerial() {
    while (coprocSerial.available() > 0) {
        const uint8_t b = (uint8_t)coprocSerial.read();
        switch (coprocRx.state) {
            case CoprocRxState::WAIT_MAGIC_1:
                if (b == (COPROC_FRAME_MAGIC & 0xFF)) coprocRx.state = CoprocRxState::WAIT_MAGIC_2;
                break;
            case CoprocRxState::WAIT_MAGIC_2:
                if (b == ((COPROC_FRAME_MAGIC >> 8) & 0xFF)) coprocRx.state = CoprocRxState::READ_TYPE;
                else coprocRx.state = CoprocRxState::WAIT_MAGIC_1;
                break;
            case CoprocRxState::READ_TYPE:
                coprocRx.type = b;
                coprocRx.state = CoprocRxState::READ_LEN_1;
                break;
            case CoprocRxState::READ_LEN_1:
                coprocRx.length = b;
                coprocRx.state = CoprocRxState::READ_LEN_2;
                break;
            case CoprocRxState::READ_LEN_2:
                coprocRx.length |= (uint16_t)b << 8;
                if (coprocRx.length > COPROC_FRAME_MAX_PAYLOAD) {
                    resetCoprocRx();
                } else if (coprocRx.length == 0) {
                    coprocRx.state = CoprocRxState::READ_CRC_1;
                } else {
                    coprocRx.payloadIndex = 0;
                    coprocRx.state = CoprocRxState::READ_PAYLOAD;
                }
                break;
            case CoprocRxState::READ_PAYLOAD:
                coprocRx.payload[coprocRx.payloadIndex++] = b;
                if (coprocRx.payloadIndex >= coprocRx.length) {
                    coprocRx.state = CoprocRxState::READ_CRC_1;
                }
                break;
            case CoprocRxState::READ_CRC_1:
                coprocRx.expectedCrc = b;
                coprocRx.state = CoprocRxState::READ_CRC_2;
                break;
            case CoprocRxState::READ_CRC_2: {
                coprocRx.expectedCrc |= (uint16_t)b << 8;
                uint8_t crcData[1 + 2 + COPROC_FRAME_MAX_PAYLOAD] = {0};
                crcData[0] = coprocRx.type;
                crcData[1] = (uint8_t)(coprocRx.length & 0xFF);
                crcData[2] = (uint8_t)((coprocRx.length >> 8) & 0xFF);
                if (coprocRx.length > 0) memcpy(crcData + 3, coprocRx.payload, coprocRx.length);
                const uint16_t actual = crc16Ccitt(crcData, coprocRx.length + 3);
                if (actual == coprocRx.expectedCrc) {
                    handleCoprocFrame(coprocRx.type, coprocRx.payload, coprocRx.length);
                }
                resetCoprocRx();
                break;
            }
        }
    }
}

static bool sendCoprocHello() {
    resetCoprocAck();
    Serial.println("[C3]  Sending HELLO to coprocessor...");
    const bool ok = sendCoprocFrame(COPROC_FRAME_HELLO, nullptr, 0);
    lastCoprocHelloAt = millis();
    return ok;
}

static void beginCoprocAwait(uint8_t frameType, unsigned long now, bool resetRetries = true) {
    nodeOtaJob.awaitingAck = true;
    nodeOtaJob.awaitingFrameType = frameType;
    nodeOtaJob.lastAckAt = now;
    if (resetRetries) nodeOtaJob.coprocAckRetries = 0;
}

static bool sendCoprocUploadBeginFrame(unsigned long now, bool resetRetries = true) {
    CoprocUploadBeginPayload payload{};
    payload.session_id = nodeOtaJob.sessionId;
    payload.image_size = (uint32_t)nodeOtaJob.imageSize;
    payload.image_crc32 = nodeOtaJob.imageCrc32;
    payload.upload_target = COPROC_UPLOAD_TARGET_NODE_HELPER;
    payload.node_type = (uint8_t)nodeOtaJob.targetType;
    payload.ap_channel = NODE_OTA_AP_CHANNEL;
    payload.port = NODE_OTA_PORT;
    strncpy(payload.version, nodeOtaJob.version, sizeof(payload.version) - 1);
    strncpy(payload.ssid, nodeOtaJob.apSsid, sizeof(payload.ssid) - 1);
    strncpy(payload.password, nodeOtaJob.apPassword, sizeof(payload.password) - 1);
    resetCoprocAck();
    if (!sendCoprocFrame(COPROC_FRAME_UPLOAD_BEGIN, &payload, sizeof(payload))) {
        return false;
    }
    beginCoprocAwait(COPROC_FRAME_UPLOAD_BEGIN, now, resetRetries);
    return true;
}

static bool sendCoprocUploadChunkFrame(unsigned long now, bool resetRetries = true, bool* reachedEnd = nullptr) {
    if (reachedEnd) *reachedEnd = false;
    if (!nodeOtaJob.file) {
        nodeOtaJob.file = LittleFS.open(NODE_OTA_FILE_PATH, "r");
        if (!nodeOtaJob.file) {
            return false;
        }
    }

    CoprocUploadChunkPayload chunk{};
    chunk.offset = (uint32_t)nodeOtaJob.uploadOffset;
    if (!nodeOtaJob.file.seek(nodeOtaJob.uploadOffset, SeekSet)) {
        return false;
    }

    const size_t n = nodeOtaJob.file.read(chunk.data, sizeof(chunk.data));
    if (n == 0) {
        if (reachedEnd) *reachedEnd = true;
        return true;
    }

    resetCoprocAck();
    if (!sendCoprocFrame(COPROC_FRAME_UPLOAD_CHUNK, &chunk, sizeof(chunk.offset) + n)) {
        return false;
    }
    beginCoprocAwait(COPROC_FRAME_UPLOAD_CHUNK, now, resetRetries);
    return true;
}

static bool sendCoprocUploadEndFrame(unsigned long now, bool resetRetries = true) {
    resetCoprocAck();
    if (!sendCoprocFrame(COPROC_FRAME_UPLOAD_END, &nodeOtaJob.sessionId, sizeof(nodeOtaJob.sessionId))) {
        return false;
    }
    beginCoprocAwait(COPROC_FRAME_UPLOAD_END, now, resetRetries);
    return true;
}

static void beginCoprocSelfOtaAwait(uint8_t frameType, unsigned long now, bool resetRetries = true) {
    coprocOtaJob.awaitingAck = true;
    coprocOtaJob.awaitingFrameType = frameType;
    coprocOtaJob.lastAckAt = now;
    if (resetRetries) coprocOtaJob.ackRetries = 0;
}

static bool sendCoprocSelfUploadBeginFrame(unsigned long now, bool resetRetries = true) {
    CoprocUploadBeginPayload payload{};
    payload.session_id = coprocOtaJob.sessionId;
    payload.image_size = (uint32_t)coprocOtaJob.imageSize;
    payload.image_crc32 = coprocOtaJob.imageCrc32;
    payload.upload_target = COPROC_UPLOAD_TARGET_SELF;
    payload.node_type = 0;
    payload.ap_channel = 0;
    payload.port = 0;
    strncpy(payload.version, coprocOtaJob.version, sizeof(payload.version) - 1);
    resetCoprocAck();
    if (!sendCoprocFrame(COPROC_FRAME_UPLOAD_BEGIN, &payload, sizeof(payload))) {
        return false;
    }
    beginCoprocSelfOtaAwait(COPROC_FRAME_UPLOAD_BEGIN, now, resetRetries);
    return true;
}

static bool sendCoprocSelfUploadChunkFrame(unsigned long now, bool resetRetries = true, bool* reachedEnd = nullptr) {
    if (reachedEnd) *reachedEnd = false;
    if (!coprocOtaJob.file) {
        coprocOtaJob.file = LittleFS.open(COPROC_OTA_FILE_PATH, "r");
        if (!coprocOtaJob.file) {
            return false;
        }
    }

    CoprocUploadChunkPayload chunk{};
    chunk.offset = (uint32_t)coprocOtaJob.uploadOffset;
    if (!coprocOtaJob.file.seek(coprocOtaJob.uploadOffset, SeekSet)) {
        return false;
    }

    const size_t n = coprocOtaJob.file.read(chunk.data, sizeof(chunk.data));
    if (n == 0) {
        if (reachedEnd) *reachedEnd = true;
        return true;
    }

    resetCoprocAck();
    if (!sendCoprocFrame(COPROC_FRAME_UPLOAD_CHUNK, &chunk, sizeof(chunk.offset) + n)) {
        return false;
    }
    beginCoprocSelfOtaAwait(COPROC_FRAME_UPLOAD_CHUNK, now, resetRetries);
    return true;
}

static bool sendCoprocSelfUploadEndFrame(unsigned long now, bool resetRetries = true) {
    resetCoprocAck();
    if (!sendCoprocFrame(COPROC_FRAME_UPLOAD_END, &coprocOtaJob.sessionId, sizeof(coprocOtaJob.sessionId))) {
        return false;
    }
    beginCoprocSelfOtaAwait(COPROC_FRAME_UPLOAD_END, now, resetRetries);
    return true;
}

static void initCoprocLink() {
    pinMode(COPROC_RESET_PIN, OUTPUT);
    digitalWrite(COPROC_RESET_PIN, LOW);
    coprocSerial.setRxBufferSize(COPROC_UART_RX_BUFFER_SIZE);
    coprocSerial.setTxBufferSize(COPROC_UART_TX_BUFFER_SIZE);
    coprocSerial.begin(COPROC_UART_BAUD, SERIAL_8N1, COPROC_UART_RX_PIN, COPROC_UART_TX_PIN);
    Serial.printf("[C3]  Coprocessor UART initialized: baud=%u RX=%u TX=%u reset=%u rxbuf=%u txbuf=%u\n",
                  (unsigned)COPROC_UART_BAUD,
                  (unsigned)COPROC_UART_RX_PIN,
                  (unsigned)COPROC_UART_TX_PIN,
                  (unsigned)COPROC_RESET_PIN,
                  (unsigned)COPROC_UART_RX_BUFFER_SIZE,
                  (unsigned)COPROC_UART_TX_BUFFER_SIZE);
    flushCoprocSerialInput();
    sendCoprocHello();
}

static void processCoprocHeartbeat(unsigned long now) {
    const bool allowHeartbeat =
        !nodeOtaJob.active &&
        (!coprocOtaJob.active || coprocOtaJob.stage == COPROC_OTA_JOB_WAIT_REBOOT);
    const unsigned long pingInterval = coprocOnline ? COPROC_LINK_PING_MS : 1500UL;
    if (allowHeartbeat && (now - lastCoprocHelloAt) >= pingInterval) {
        sendCoprocHello();
    }

    const bool jobAwaitingHello =
        (nodeOtaJob.active && nodeOtaJob.awaitingAck && nodeOtaJob.awaitingFrameType == COPROC_FRAME_HELLO) ||
        (coprocOtaJob.active && coprocOtaJob.awaitingAck && coprocOtaJob.awaitingFrameType == COPROC_FRAME_HELLO);

    if (coprocAck.ready && coprocAck.originalType == COPROC_FRAME_HELLO && !jobAwaitingHello) {
        const bool wasOnline = coprocOnline;
        coprocOnline = coprocAck.ok;
        lastCoprocAckAt = now;
        lastCoprocNoAckLogAt = 0;
        if (coprocOnline) lastCoprocRecoveryPulseAt = 0;
        if (coprocOnline && !wasOnline) {
            Serial.println("[C3]  Coprocessor helper online.");
            broadcastMetaIfClientsConnected();
        }
        resetCoprocAck();
    }

    if (!coprocOnline && lastCoprocHelloAt > 0 && (now - lastCoprocHelloAt) > COPROC_ACK_TIMEOUT_MS) {
        if (lastCoprocNoAckLogAt == 0 || (now - lastCoprocNoAckLogAt) > 5000UL) {
            Serial.println("[C3]  No HELLO response from coprocessor yet.");
            lastCoprocNoAckLogAt = now;
        }

        const unsigned long recoveryAge = (lastCoprocAckAt > 0) ? (now - lastCoprocAckAt) : (now - lastCoprocHelloAt);
        if (allowHeartbeat &&
            recoveryAge >= COPROC_RECOVERY_REBOOT_MS &&
            (lastCoprocRecoveryPulseAt == 0 ||
             (now - lastCoprocRecoveryPulseAt) >= COPROC_RECOVERY_COOLDOWN_MS)) {
            Serial.println("[C3]  Coprocessor still offline. Requesting helper reboot and resetting the UART parser.");
            flushCoprocSerialInput();
            requestCoprocReboot();
            lastCoprocHelloAt = now;
        }
    }

    if (coprocOnline && allowHeartbeat && lastCoprocAckAt > 0 &&
        (now - lastCoprocAckAt) > (COPROC_LINK_PING_MS * 3)) {
        coprocOnline = false;
        Serial.println("[C3]  Coprocessor helper heartbeat lost.");
        broadcastMetaIfClientsConnected();
    }
}

static bool sendNodeOtaBegin(uint8_t nodeId, uint8_t attempt = 1) {
    if (nodeId == 0 || nodeId >= nextId) return false;
    if (nodes[nodeId].mac[0] == 0) return false;

    MsgNodeOtaBegin msg{};
    msg.hdr.type = MSG_NODE_OTA_BEGIN;
    msg.hdr.node_id = nodeId;
    msg.hdr.node_type = nodes[nodeId].type;
    msg.session_id = nodeOtaJob.sessionId;
    msg.image_size = (uint32_t)nodeOtaJob.imageSize;
    msg.image_crc32 = nodeOtaJob.imageCrc32;
    msg.port = NODE_OTA_PORT;
    strncpy(msg.ssid, nodeOtaJob.apSsid, sizeof(msg.ssid) - 1);
    strncpy(msg.password, nodeOtaJob.apPassword, sizeof(msg.password) - 1);
    strncpy(msg.version, nodeOtaJob.version, sizeof(msg.version) - 1);

    const esp_err_t err = esp_now_send(nodes[nodeId].mac, reinterpret_cast<uint8_t*>(&msg), sizeof(msg));
    if (err != ESP_OK) {
        Serial.printf("[NODE OTA]  Failed to send OTA begin to node #%u on attempt %u\n", nodeId, attempt);
        return false;
    }

    Serial.printf("[NODE OTA]  Sent OTA begin to node #%u (%s) attempt %u\n",
                  nodeId, macToStr(nodes[nodeId].mac).c_str(), attempt);
    return true;
}
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
void loop() {
    unsigned long now = millis();

    processGatewayFactoryResetButton(now);
    processRxQueue();
    now = millis();
    processCoprocSerial();
    processCoprocHeartbeat(now);
    processNodeOtaJob(now);
    processCoprocOtaJob(now);
    processGatewayNetworkState(now);
    refreshTimedOutNodes(now);
    sampleGatewayBuiltinSensorIfDue(now);
    processMqtt(now);
    updateGwLed();

    if (otaRebootPending && now >= otaRebootAtMs) {
        otaRebootPending = false;
        Serial.println("[OTA]  Rebooting into updated gateway firmware.");
        delay(100);
        ESP.restart();
    }

    if (nodeRegistryDirty && (now - nodeRegistryDirtyAtMs) >= NODE_REGISTRY_FLUSH_MS) {
        saveNodesToNvs();
    }

    // Pending pair: retry PAIR_CMD until MSG_REGISTER arrives or timeout expires
    if (pendingPair.active) {
        if (now - pendingPair.startedAt > PAIR_CMD_TIMEOUT_MS) {
            pendingPair.active = false;
            Serial.println("[PAIR]  Timed out - no response from node.");
            wsBroadcast("{\"type\":\"pair_timeout\"}");
        } else if (now - pendingPair.lastAttempt >= PAIR_CMD_RETRY_MS) {
            pendingPair.lastAttempt = now;
            sendPairCmd(pendingPair.mac);
            Serial.printf("[PAIR]  Sending PAIR_CMD -> %02X:%02X:%02X:%02X:%02X:%02X\n",
                          pendingPair.mac[0], pendingPair.mac[1], pendingPair.mac[2],
                          pendingPair.mac[3], pendingPair.mac[4], pendingPair.mac[5]);
        }
    }

    // Periodic WS pushes
    if (now - lastNodeBcast >= WS_UPDATE_MS) {
        lastNodeBcast = now;
        if (ws.count() > 0) wsBroadcast(buildNodesJson());
    }
    if (now - lastMetaBcast >= WS_META_MS) {
        lastMetaBcast = now;
        if (ws.count() > 0) wsBroadcast(buildMetaJson());
    }

    // Periodic discovered list push (keeps clients in sync)
    if (now - lastDiscBcast >= WS_UPDATE_MS) {
        lastDiscBcast = now;
        if (ws.count() > 0) wsBroadcast(buildDiscoveredJson());
    }

    // Periodic discovered list cleanup (removes stale entries 
    // for nodes that disappeared without cleanly unregistering)
    if (now - lastDiscClean >= DISCOVERED_CLEANUP_MS) {
        lastDiscClean = now;
        if (cleanupDiscovered() && ws.count() > 0)
            wsBroadcast(buildDiscoveredJson());
    }

    ws.cleanupClients();
    delay(10);
}
